Inventoteca/DisplayErgonomia/Diagramas/DiagramaDisplayErgonomia.png

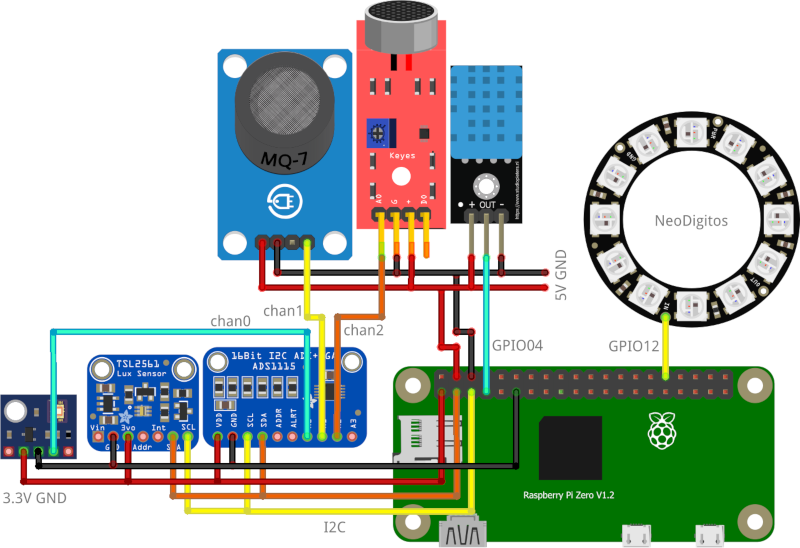
Diagramas/DiagramaDisplayErgonomia.png
