Inventoteca/DisplayErgonomia/Fotos/34:94:54:C7:D3:98.png

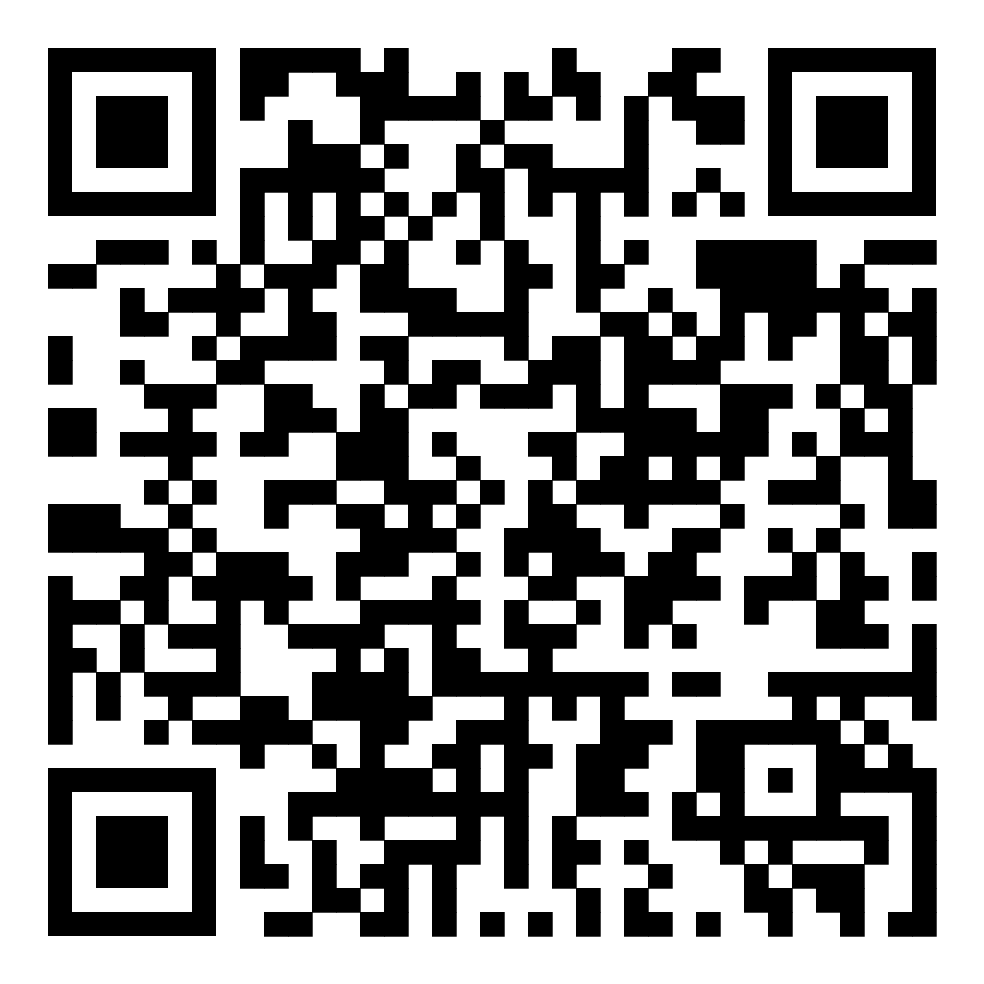
Fotos/34:94:54:C7:D3:98.png
