Inventoteca/DisplayErgonomia/Fotos/Dibujo ventanas en la parte superior.jpg

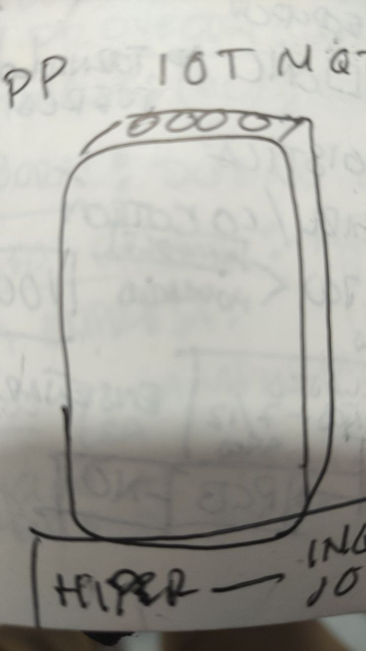
Fotos/Dibujo ventanas en la parte superior.jpg
