Inventoteca/DisplayErgonomia/Fotos/Doble capa MDF.jpg

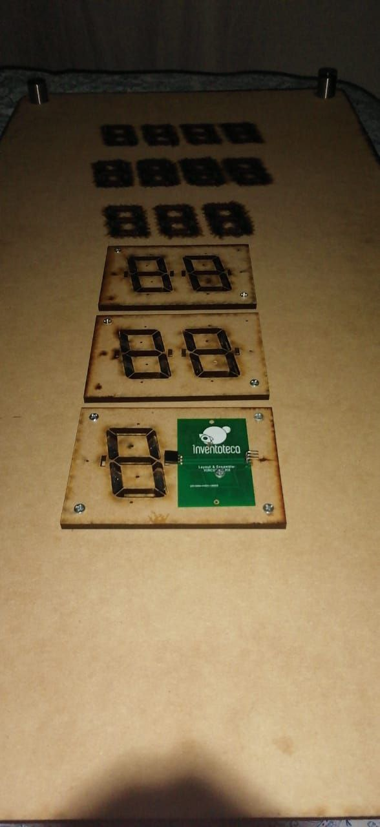
Fotos/Doble capa MDF.jpg
