Inventoteca/DisplayErgonomia/Fotos/E05A1B560F74.png

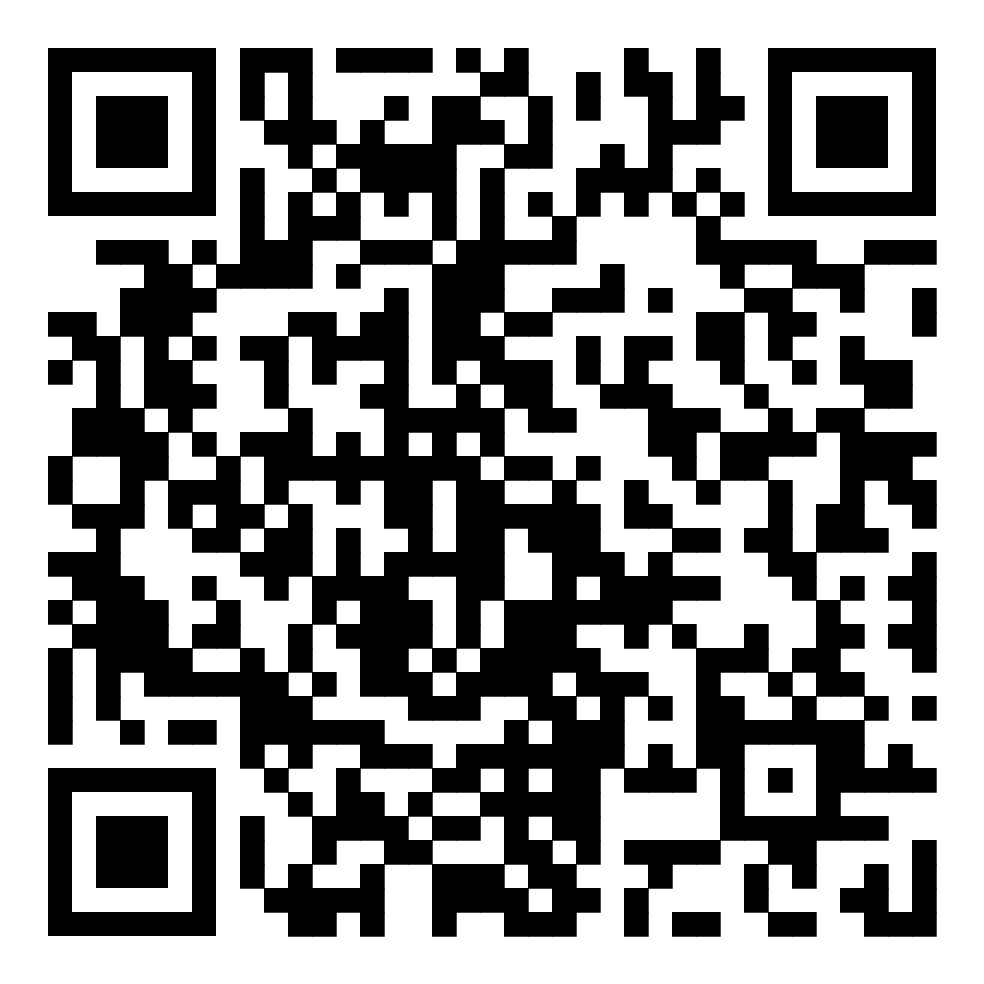
Fotos/E05A1B560F74.png
