Inventoteca/DisplayErgonomia/Fotos/E05A1B561050.png

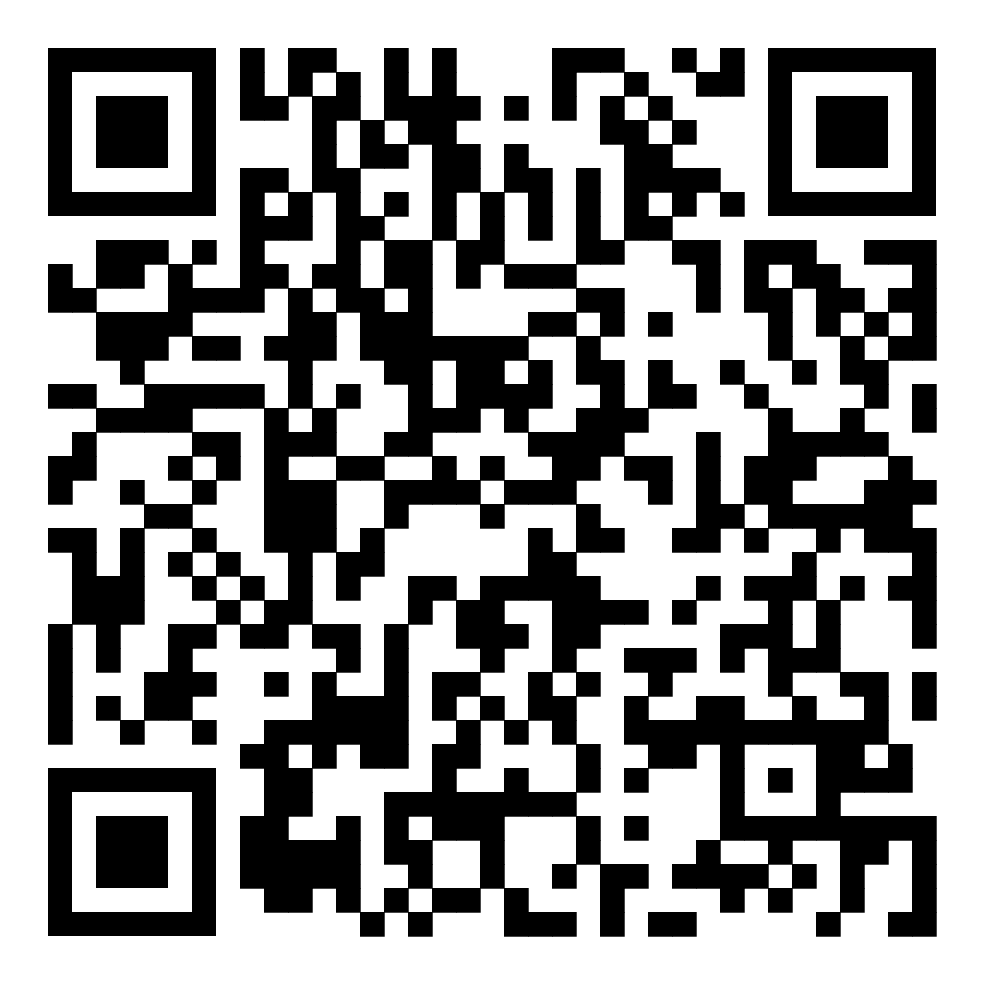
Fotos/E05A1B561050.png
