Inventoteca/DisplayErgonomia/Fotos/photo_5015306214770322337_y.jpg

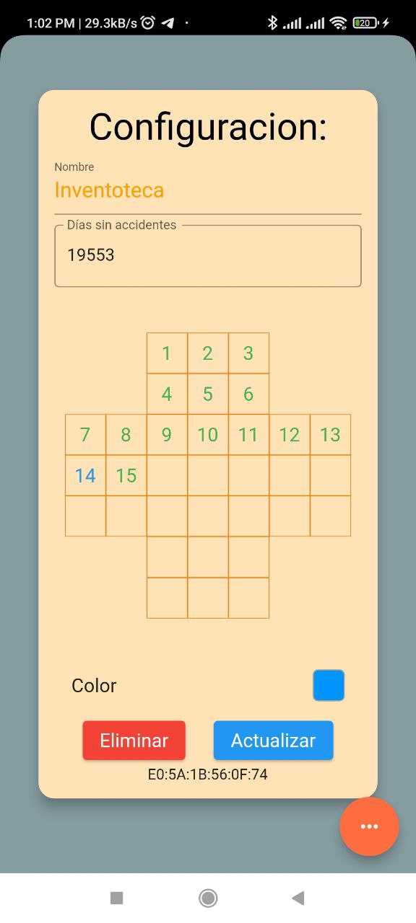
Fotos/photo_5015306214770322337_y.jpg
