Inventoteca/DisplayErgonomia/Fotos/photo_5015306214770322338_y.jpg

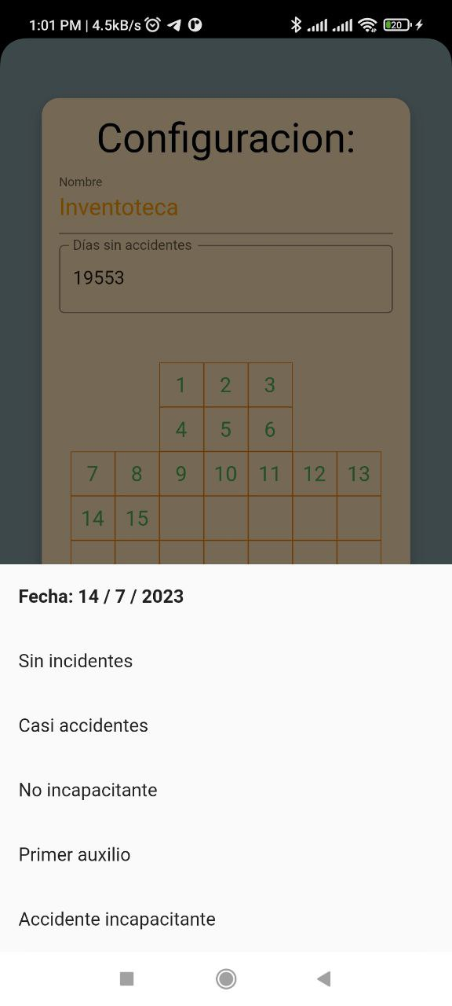
Fotos/photo_5015306214770322338_y.jpg
