Inventoteca/DisplayErgonomia/Fotos/photo_5015306214770322340_y.jpg

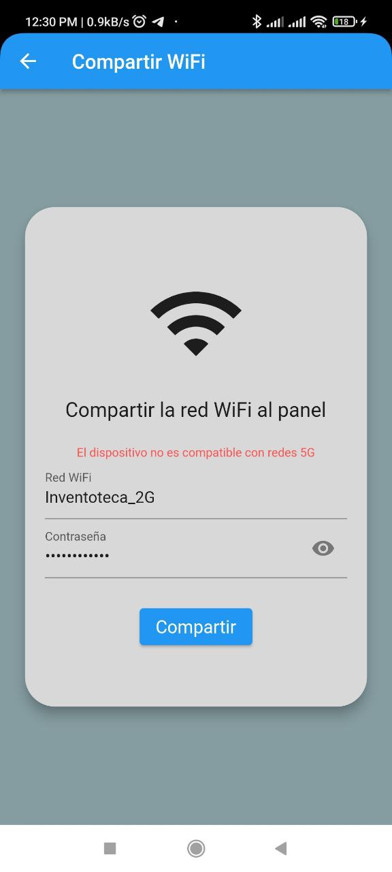
Fotos/photo_5015306214770322340_y.jpg
