Inventoteca/DisplayErgonomia/Fotos/photo_5015306214770322341_y.jpg

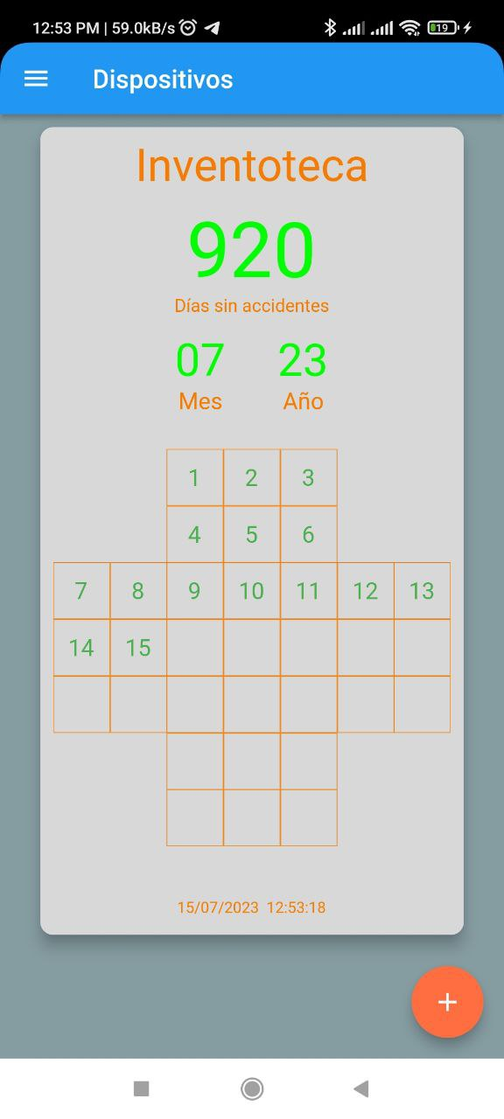
Fotos/photo_5015306214770322341_y.jpg
