Inventoteca/DisplayErgonomia/Fotos/photo_5015306214770322343_y.jpg

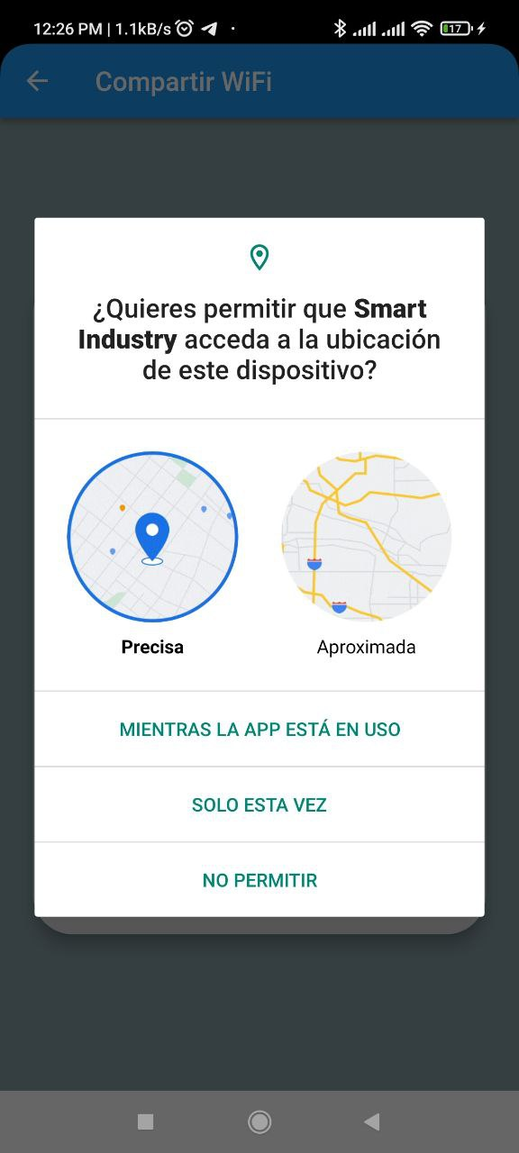
Fotos/photo_5015306214770322343_y.jpg
