Inventoteca/DisplayErgonomia/Fotos/photo_5015306214770322344_y.jpg

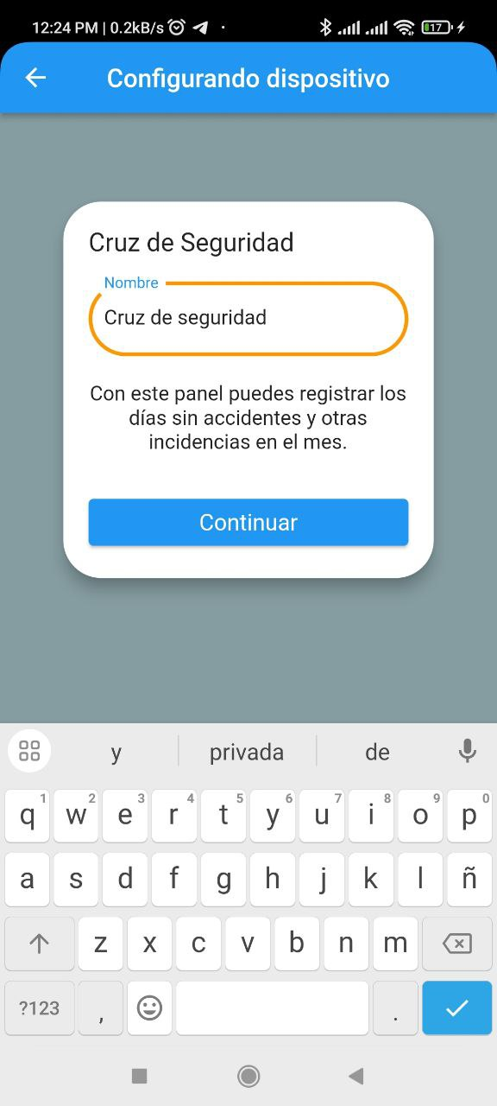
Fotos/photo_5015306214770322344_y.jpg
