Inventoteca/DisplayErgonomia/Fotos/photo_5015306214770322345_y.jpg

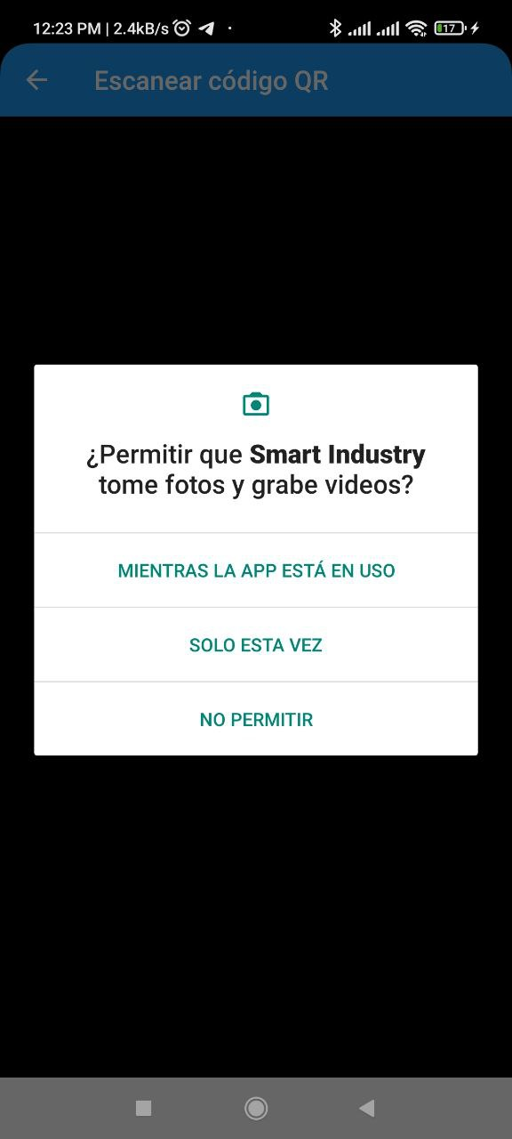
Fotos/photo_5015306214770322345_y.jpg
