Inventoteca/DisplayErgonomia/Fotos/photo_5015306214770322346_y.jpg

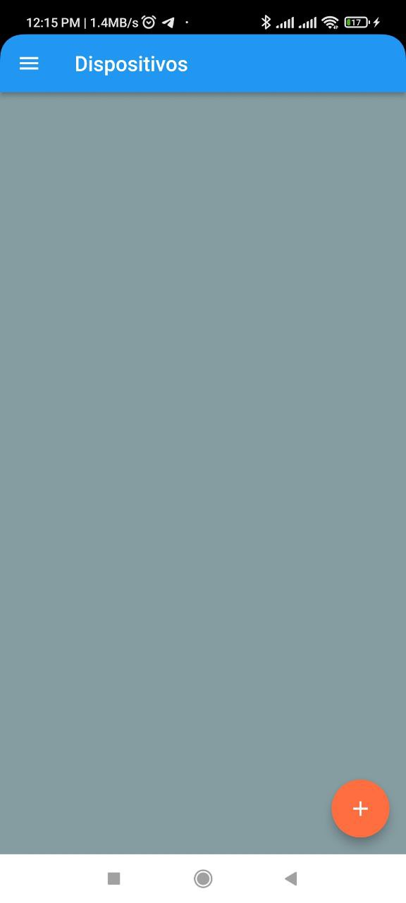
Fotos/photo_5015306214770322346_y.jpg
