Inventoteca/DisplayErgonomia/Fotos/photo_5015306214770322347_y.jpg

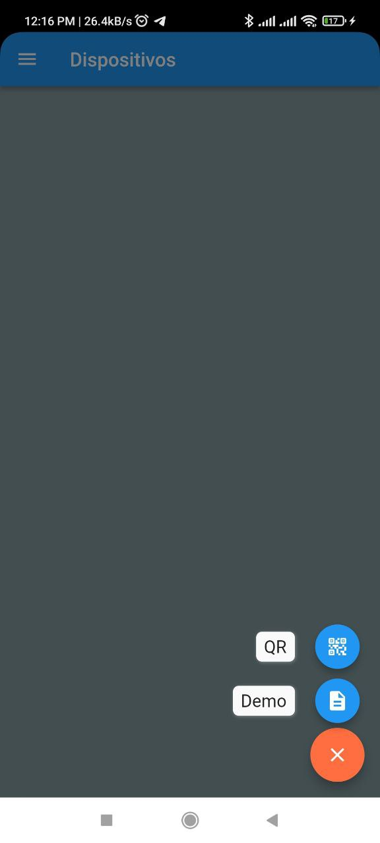
Fotos/photo_5015306214770322347_y.jpg
