Inventoteca/DisplayErgonomia/Fotos/photo_5015306214770322348_y.jpg

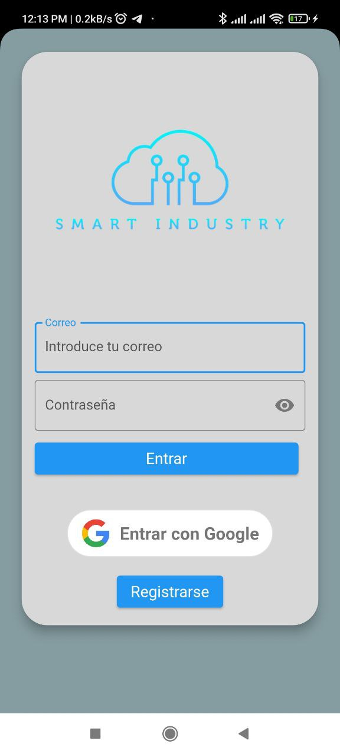
Fotos/photo_5015306214770322348_y.jpg
