Inventoteca/DisplayErgonomia/Fotos/Probando_sensores_con_Arduino/20210329_135027.jpg

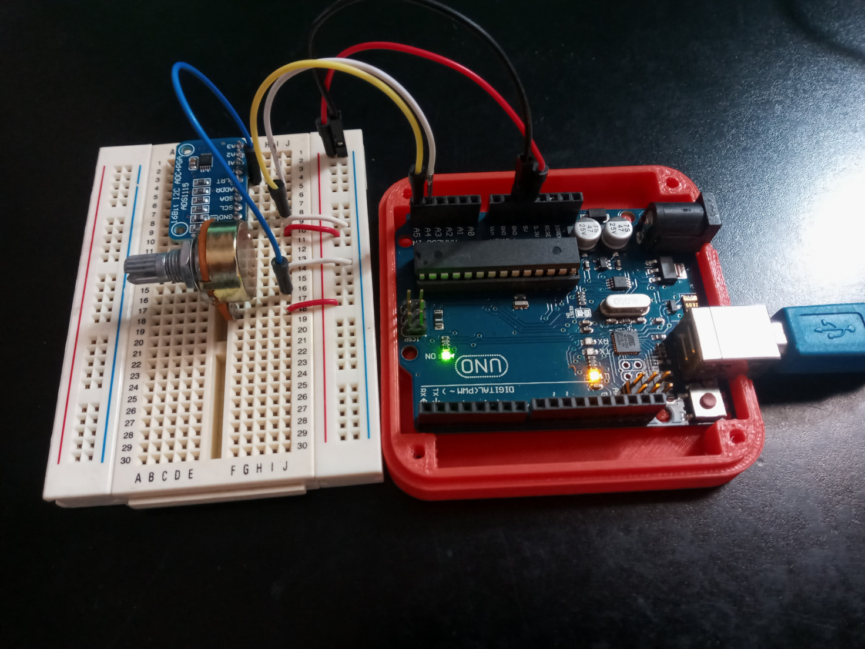
Fotos/Probando_sensores_con_Arduino/20210329_135027.jpg
