Inventoteca/DisplayErgonomia/Fotos/Probando_sensores_con_Arduino/20210329_150442.jpg

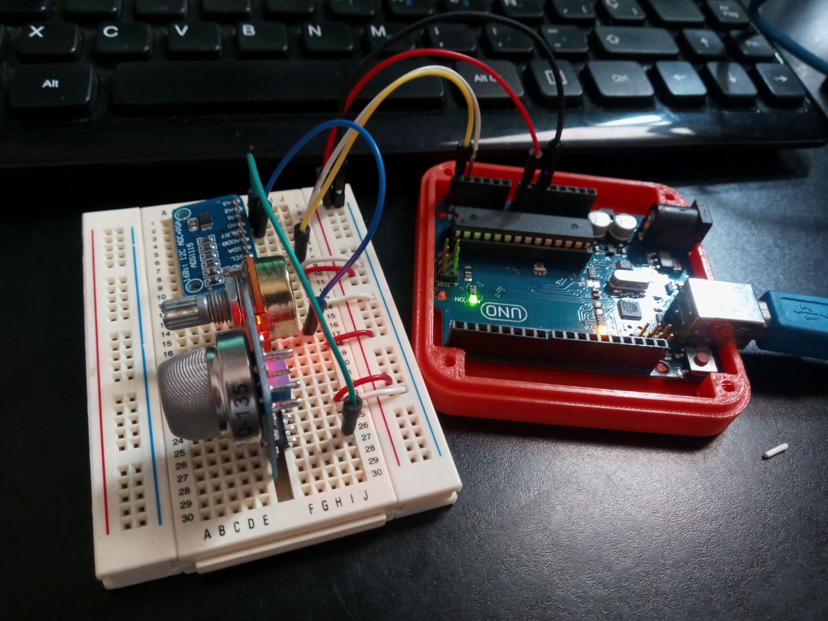
Fotos/Probando_sensores_con_Arduino/20210329_150442.jpg
