Inventoteca/DisplayErgonomia/Fotos/Probando_sensores_con_Arduino/20210329_164652.jpg

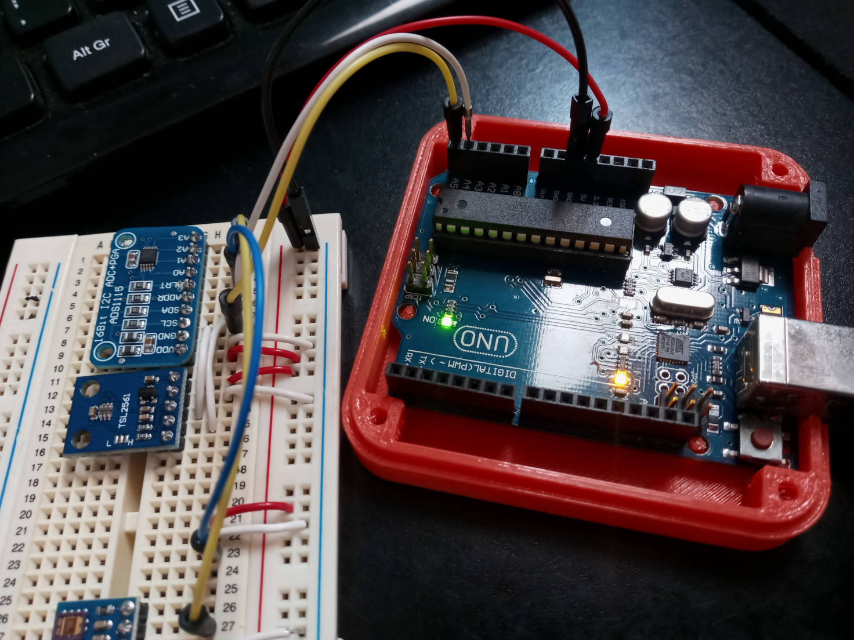
Fotos/Probando_sensores_con_Arduino/20210329_164652.jpg
