Inventoteca/DisplayErgonomia/Fotos/qr.png

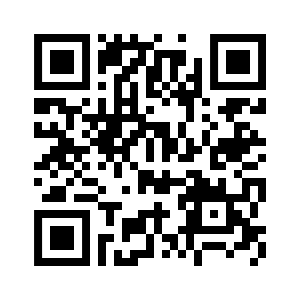
Fotos/qr.png
