Inventoteca/DisplayErgonomia/Fotos/rangos_y_colores.jpg

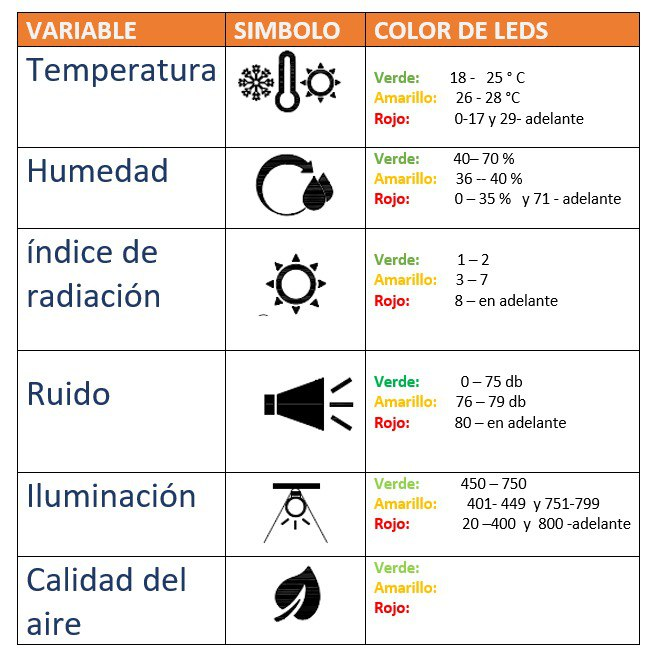
Fotos/rangos_y_colores.jpg
