Inventoteca/DisplayErgonomia/Fotos/Smart (1).png

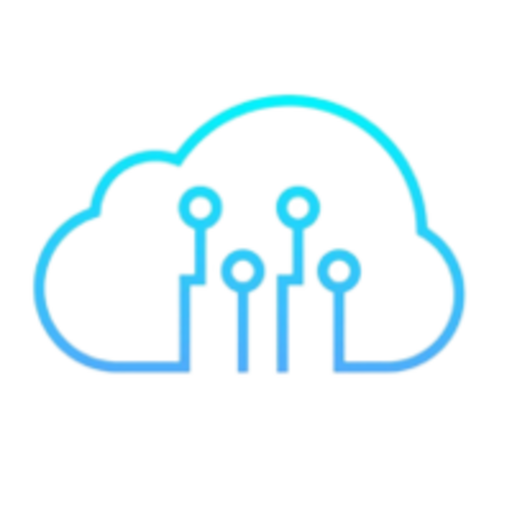
Fotos/Smart (1).png
