Inventoteca/DisplayErgonomia/Fotos/SmartIndustry.png

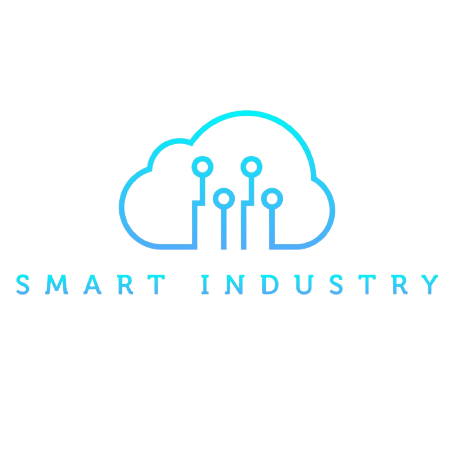
Fotos/SmartIndustry.png
