Inventoteca/DisplayErgonomia/Fotos/Vista frontal.jpg

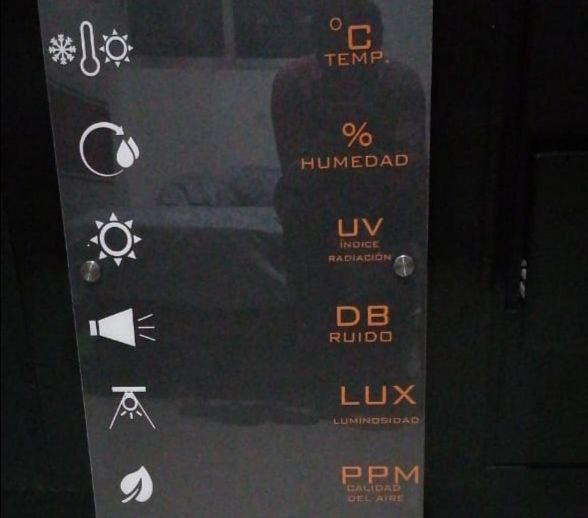
Fotos/Vista frontal.jpg
