Inventoteca/DisplayErgonomia/Programa/Capturas/ADS1115 con Arduino.png

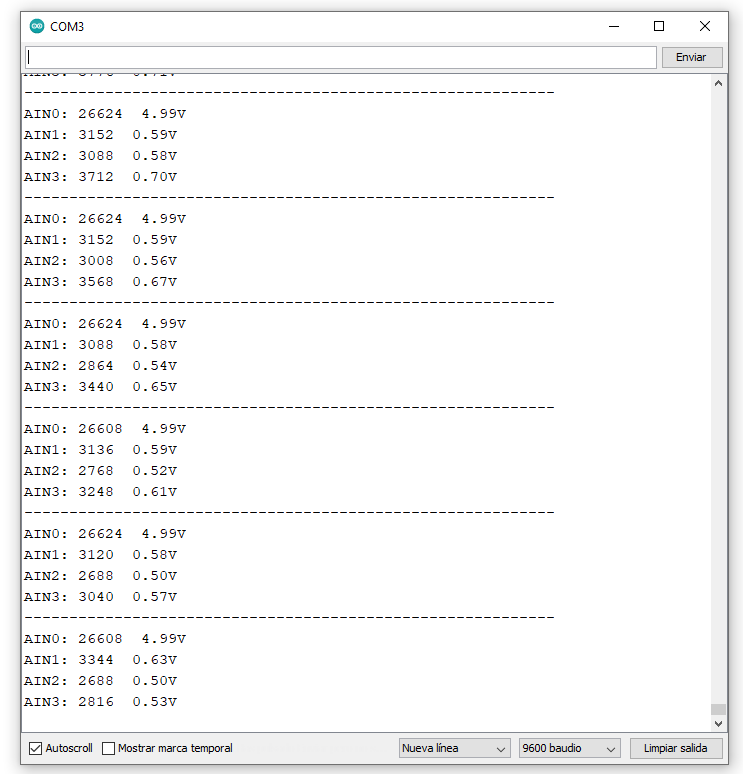
Programa/Capturas/ADS1115 con Arduino.png
