Inventoteca/DisplayErgonomia/Programa/Capturas/Captura de pantalla 2021-03-29 205107.png

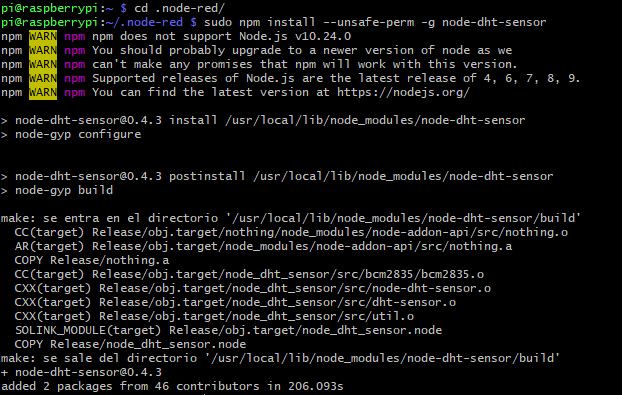
Programa/Capturas/Captura de pantalla 2021-03-29 205107.png
