Inventoteca/DisplayErgonomia/Programa/Capturas/flujo funcionando.png

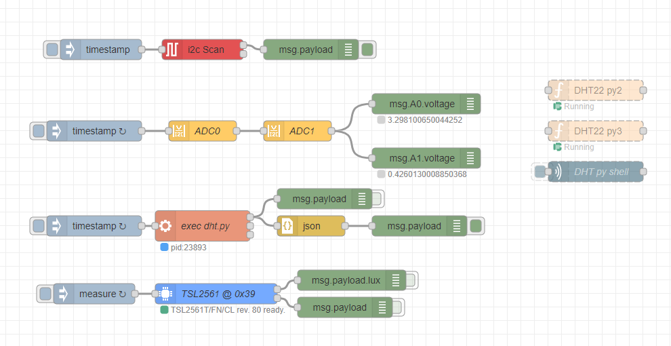
Programa/Capturas/flujo funcionando.png
