Inventoteca/DisplayErgonomia/Programa/Capturas/flujo, no ha funcionado dht, empezar a probar tsl2561.png

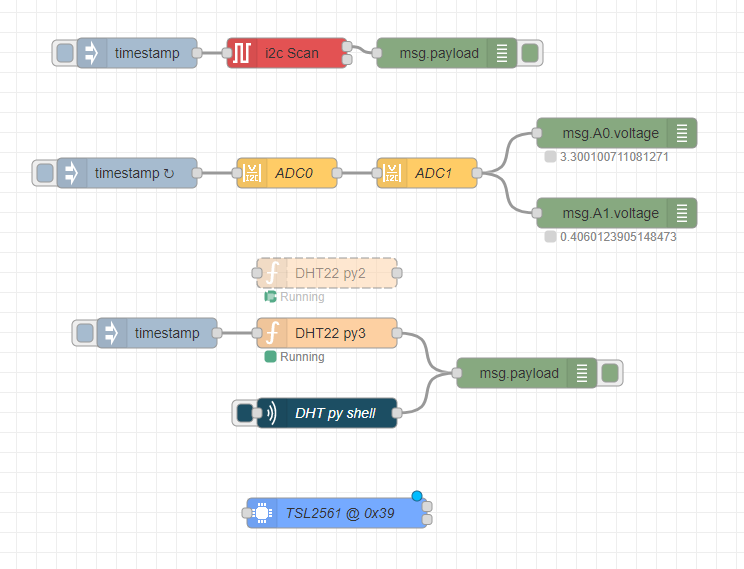
Programa/Capturas/flujo, no ha funcionado dht, empezar a probar tsl2561.png
