Inventoteca/DisplayErgonomia/Programa/Capturas/Librerías para ADS1115.png

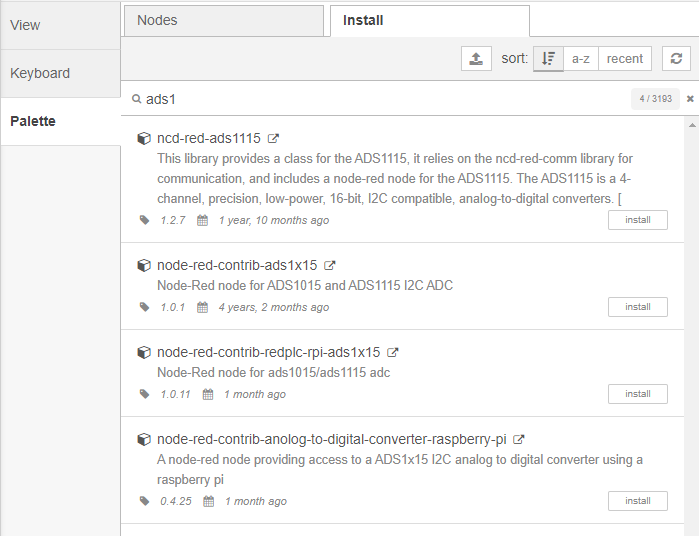
Programa/Capturas/Librerías para ADS1115.png
