Inventoteca/DisplayErgonomia/Programa/Capturas/Librerías para DHT22.png

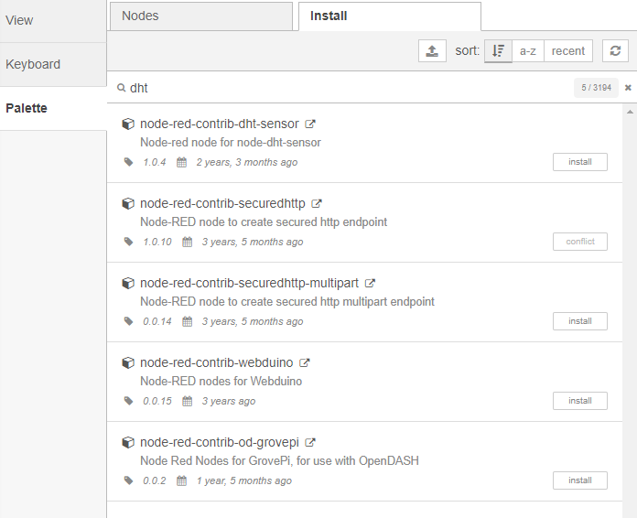
Programa/Capturas/Librerías para DHT22.png
