Inventoteca/DisplayErgonomia/Programa/Capturas/Librerías para TSL2561.png

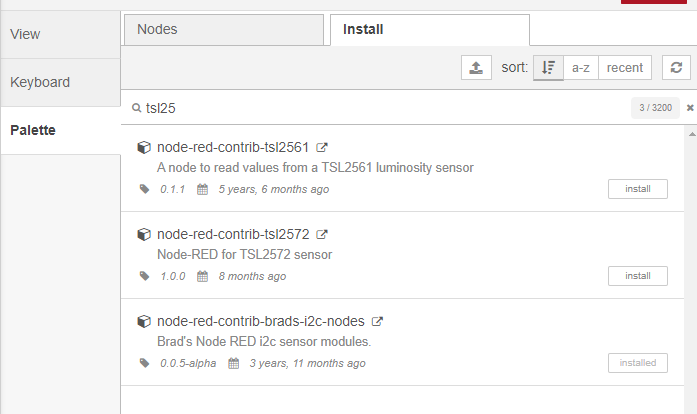
Programa/Capturas/Librerías para TSL2561.png
