Inventoteca/DisplayErgonomia/Programa/Capturas/nodos python instalados.png

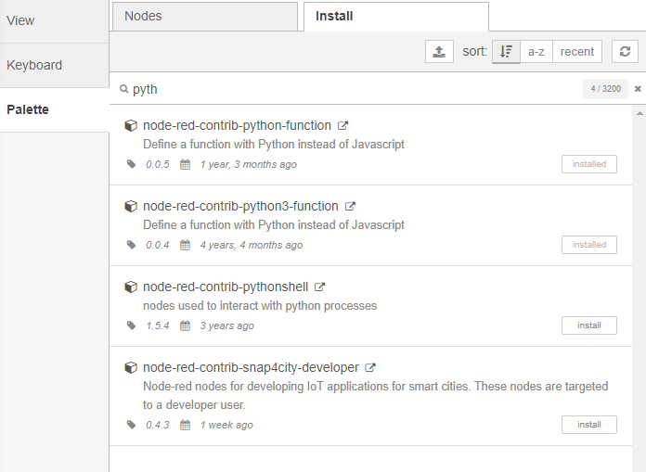
Programa/Capturas/nodos python instalados.png
