Inventoteca/DisplayErgonomia/Programa/Capturas/nr flujos y cred.png

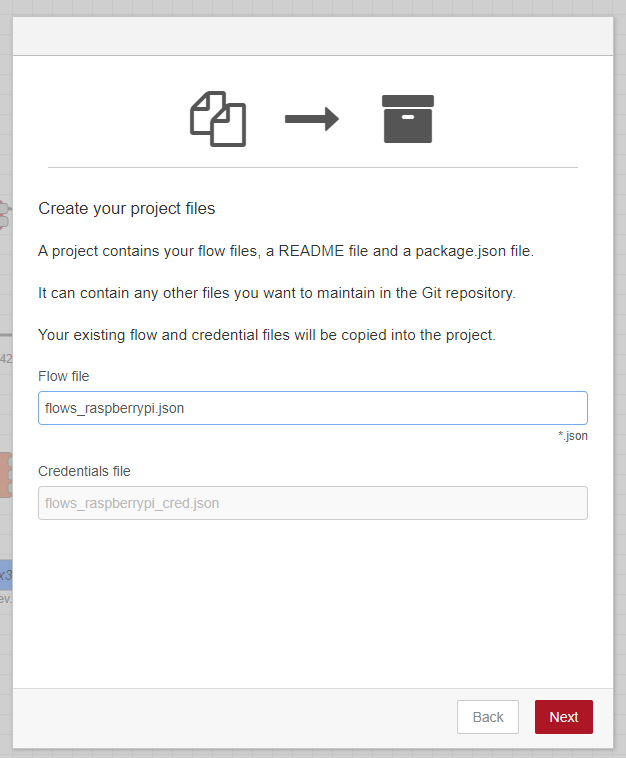
Programa/Capturas/nr flujos y cred.png
