Inventoteca/DisplayErgonomia/Programa/Capturas/nr proy.png

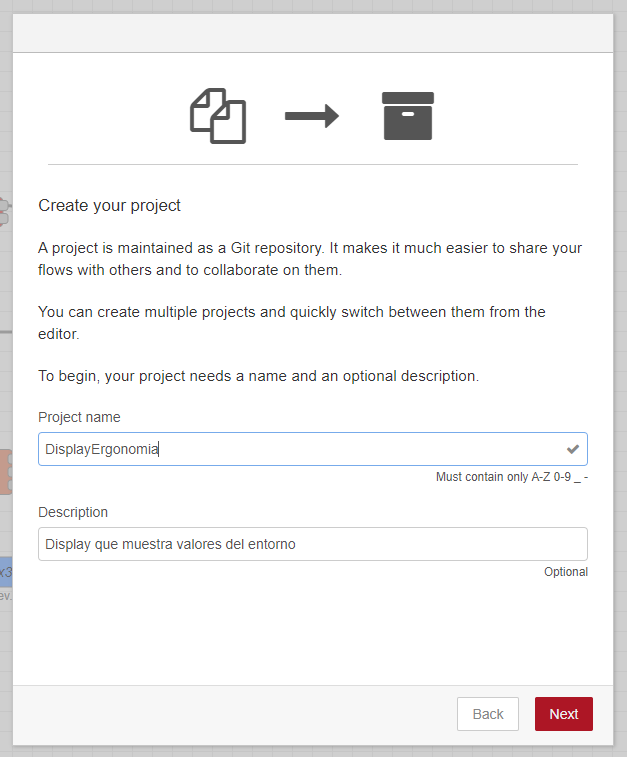
Programa/Capturas/nr proy.png
