Inventoteca/DisplayErgonomia/Programa/Capturas/nr proyecto creado.png

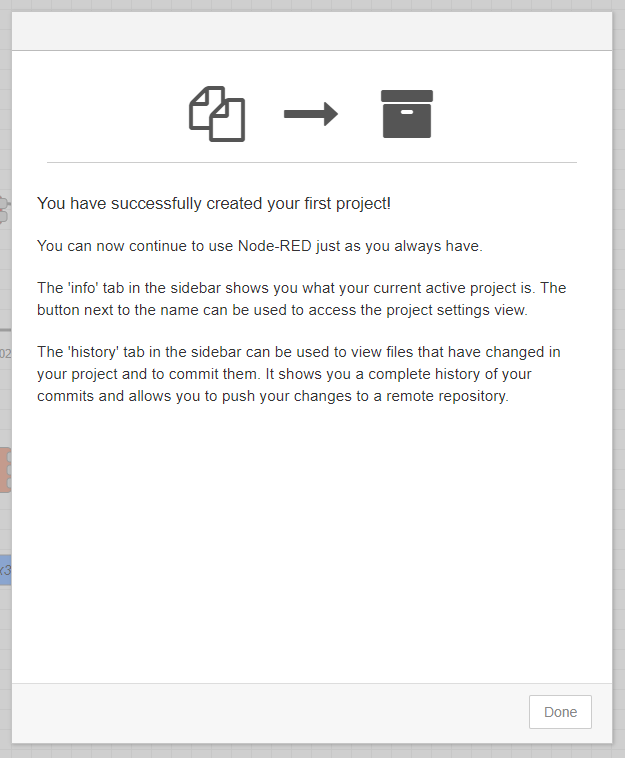
Programa/Capturas/nr proyecto creado.png
