Inventoteca/DisplayErgonomia/Programa/Capturas/nr sin ecrip.png

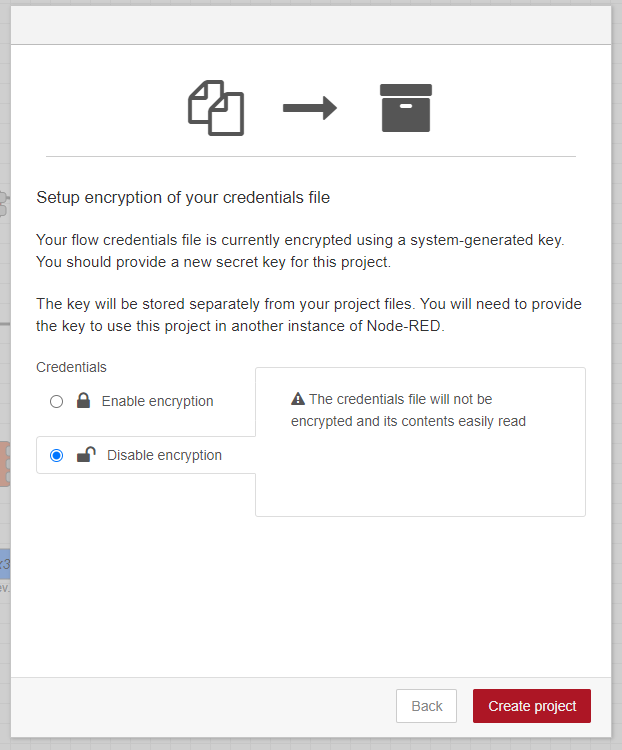
Programa/Capturas/nr sin ecrip.png
