Inventoteca/DisplayErgonomia/Programa/Capturas/nr usuario.png

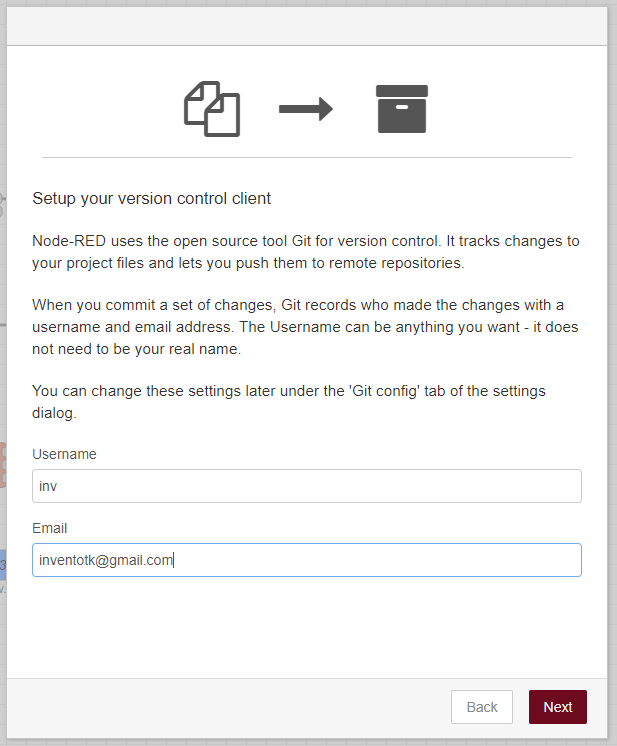
Programa/Capturas/nr usuario.png
