Inventoteca/DisplayErgonomia/Programa/Capturas/push to main.png

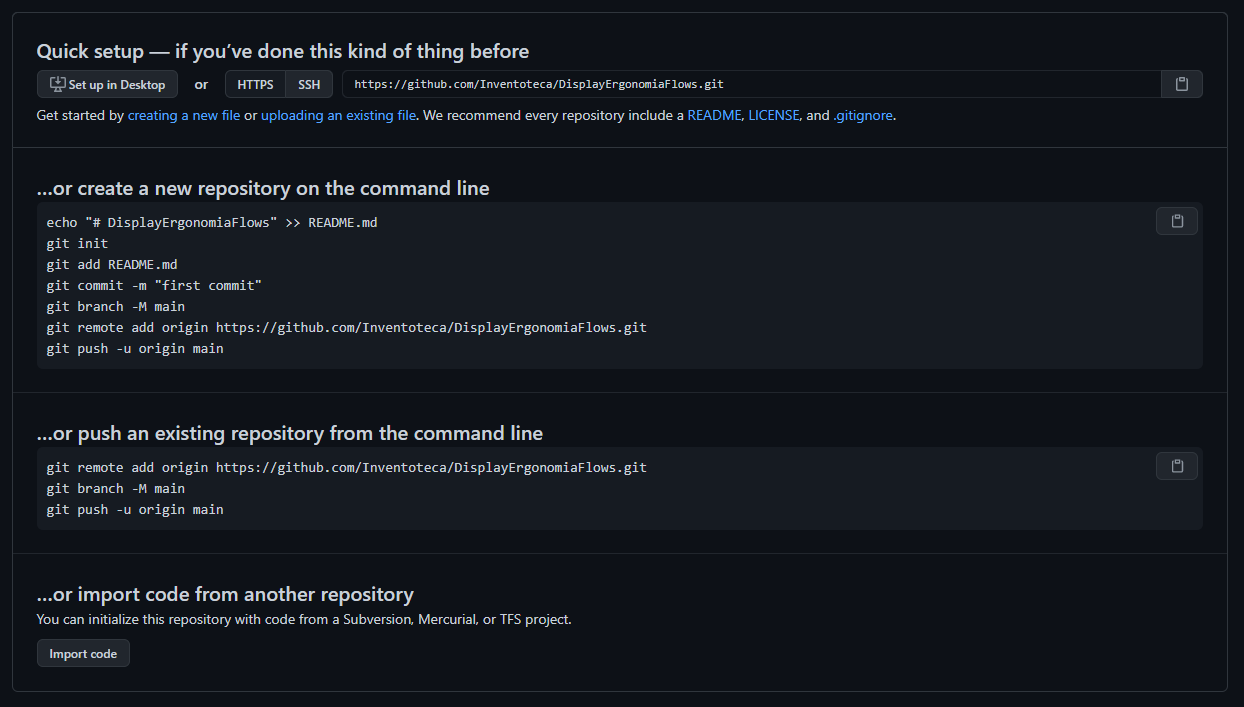
Programa/Capturas/push to main.png
