Inventoteca/DisplayErgonomia/Programa/Capturas/tsl2561 si jala.png

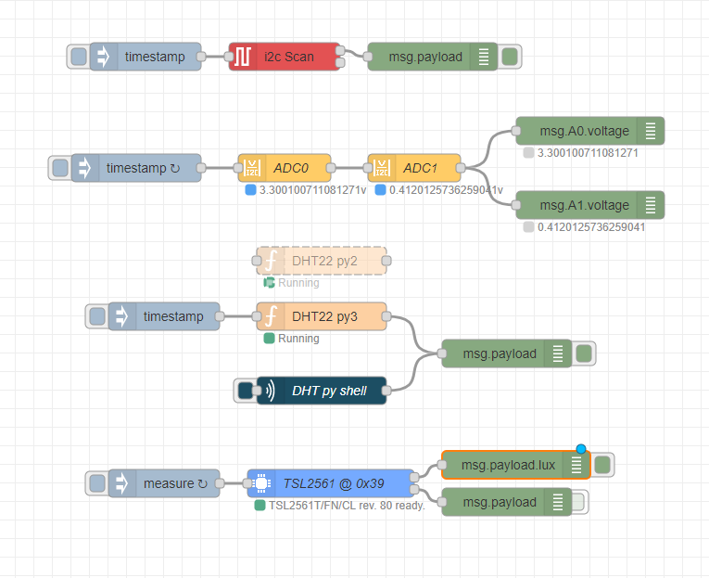
Programa/Capturas/tsl2561 si jala.png
