Inventoteca/DisplayErgonomia/Diseños/corte_laser/pasado/2digitos/2digitos_mdf3mm_126x202.dxf

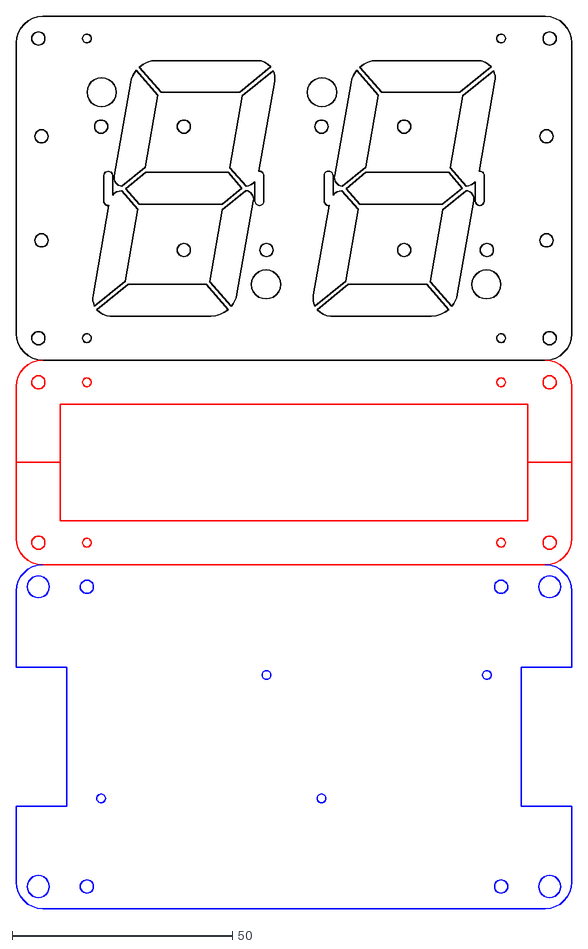
[picture p60: CAD file, 2021-03-31]
Diseños/corte_laser/pasado/2digitos/2digitos_mdf3mm_126x202.dxf
126.0 x 202.4
