Inventoteca/DisplayErgonomia/Diseños/corte_laser/pasado/3digitos/3digitos_mdf3mm_176x202.dxf

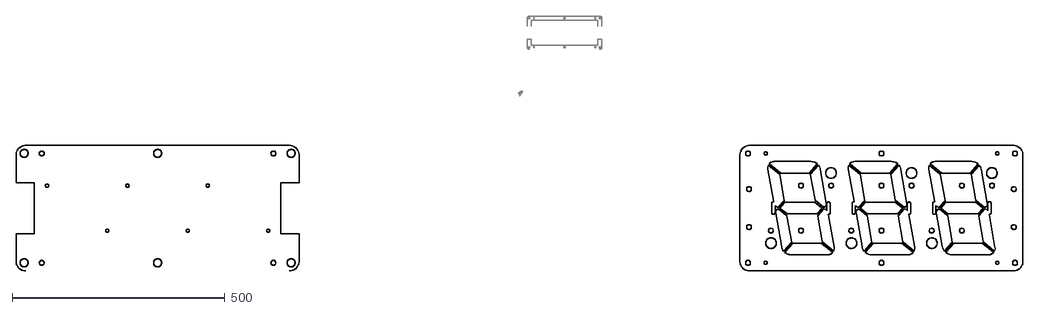
[picture p61: CAD file, 2021-03-31]
Diseños/corte_laser/pasado/3digitos/3digitos_mdf3mm_176x202.dxf
2366.0 x 598.5
