Inventoteca/DisplayErgonomia/Diseños/corte_laser/pasado/4digitos/4digitos_mdf3mm_226x202.dxf

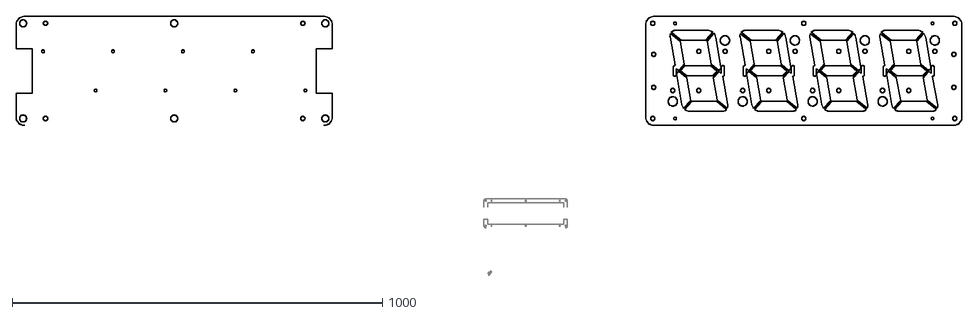
[picture p62: CAD file, 2021-03-31]
Diseños/corte_laser/pasado/4digitos/4digitos_mdf3mm_226x202.dxf
2555.0 x 700.4
