Inventoteca/DisplayErgonomia/Diseños/STL/clip.stl

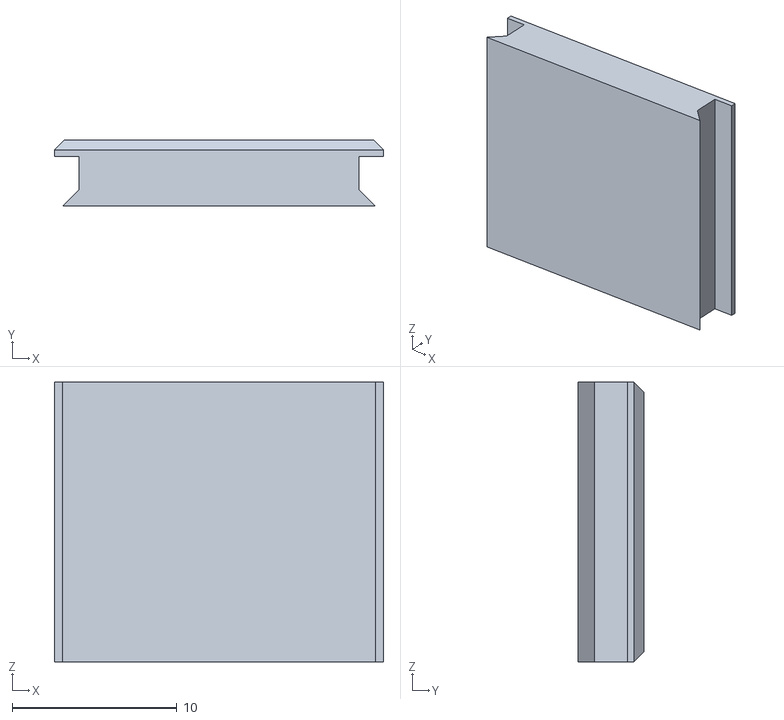
[picture p63: CAD file, 2021-07-01]
Diseños/STL/clip.stl
20.0 x 4.00 x 17.0
