Inventoteca/DisplayErgonomia/Diseños/STL/tapasen.stl

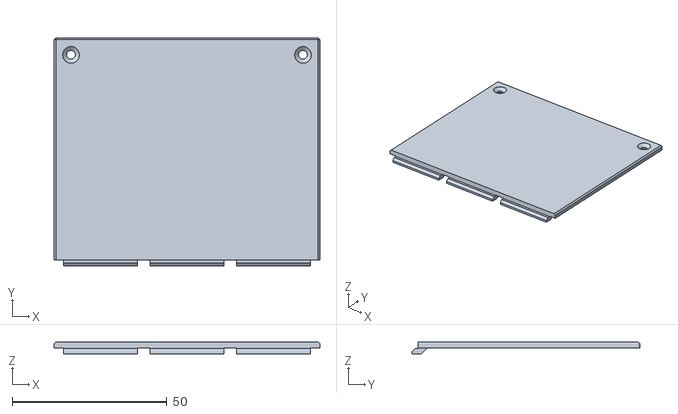
[picture p64: CAD file, 2021-07-01]
Diseños/STL/tapasen.stl
86.0 x 73.8 x 4.00
