Inventoteca/DisplayErgonomia/Diseños/STL/sopext2.stl

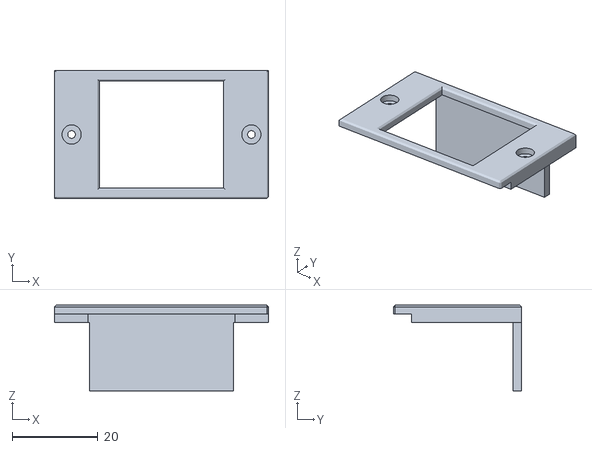
[picture p65: CAD file, 2021-07-01]
Diseños/STL/sopext2.stl
50.0 x 30.0 x 20.0
