Inventoteca/DisplayErgonomia/Fotos/Ensamblando_display/20210401_191805.jpg

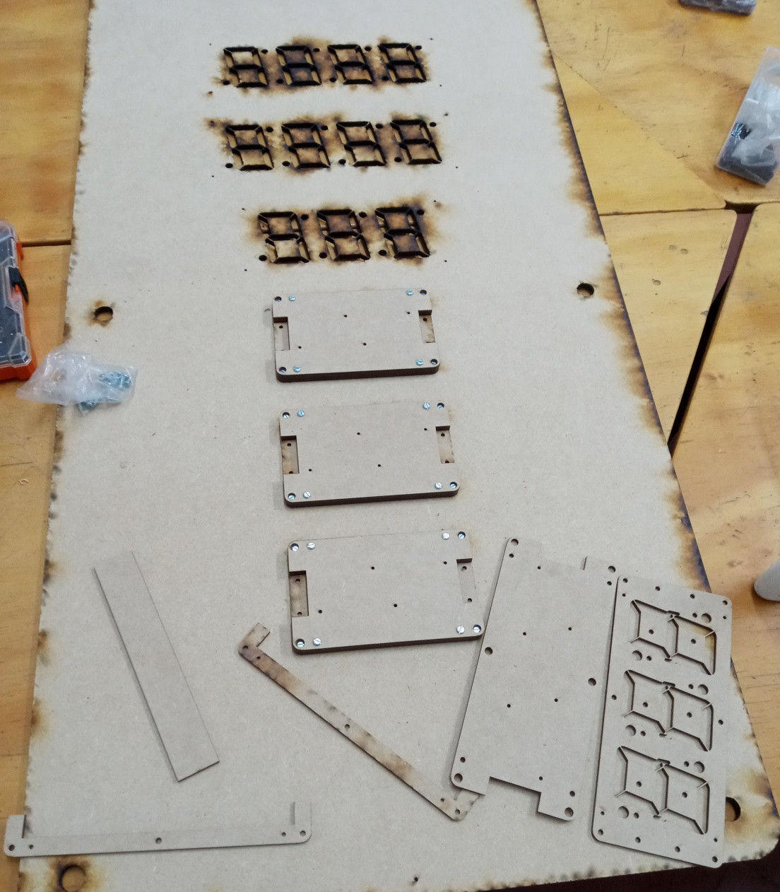
Fotos/Ensamblando_display/20210401_191805.jpg
