Inventoteca/DisplayErgonomia/Fotos/Ensamblando_display/20210401_191921.jpg

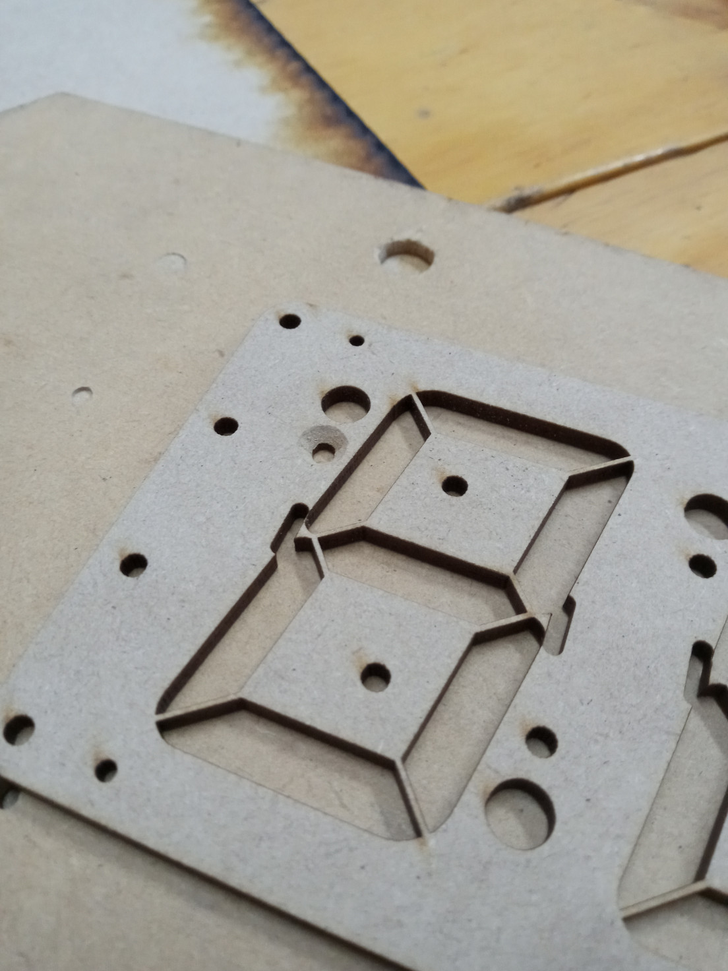
Fotos/Ensamblando_display/20210401_191921.jpg
