Inventoteca/DisplayErgonomia/Fotos/Ensamblando_display/20210401_191934.jpg

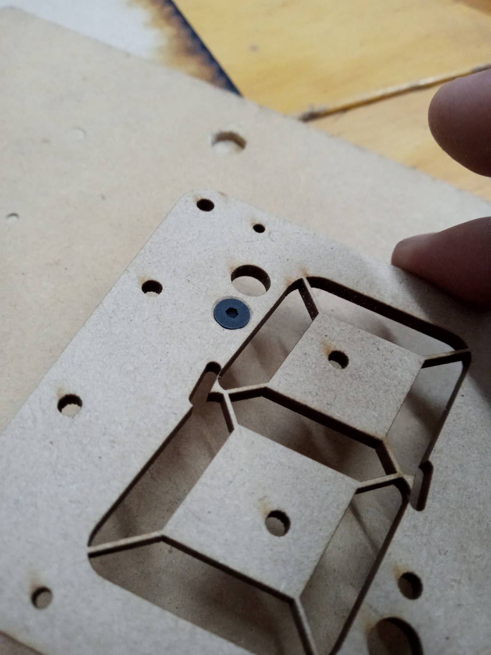
Fotos/Ensamblando_display/20210401_191934.jpg
