Inventoteca/DisplayErgonomia/Fotos/Ensamblando_display/20210401_192517.jpg

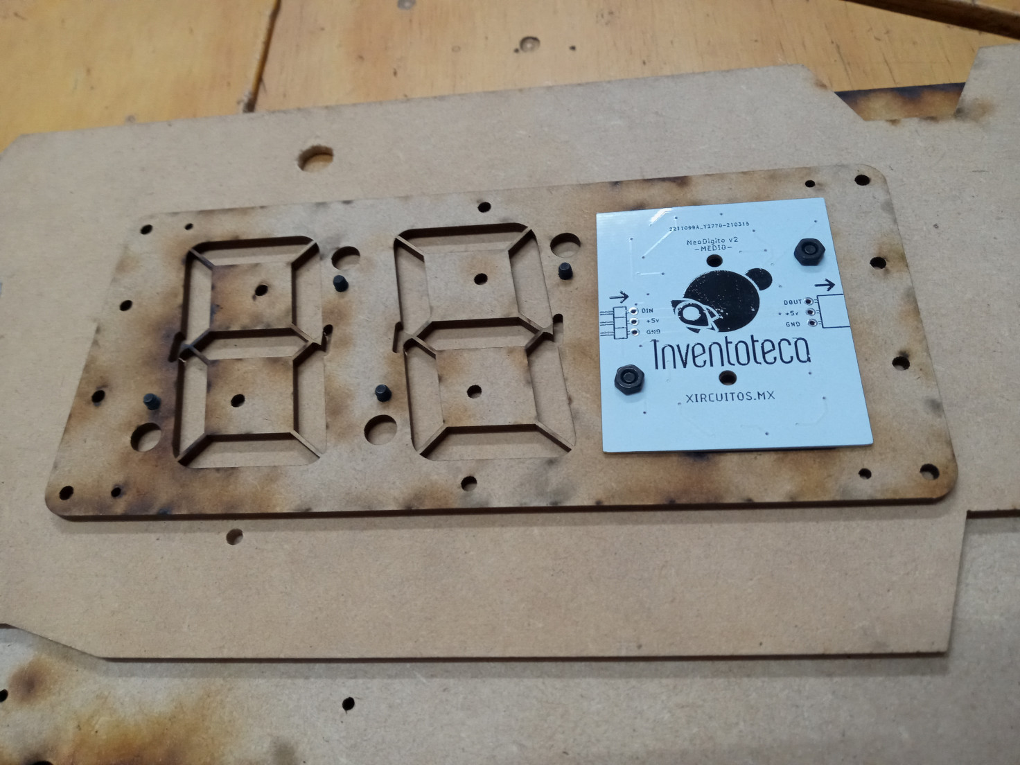
Fotos/Ensamblando_display/20210401_192517.jpg
