Inventoteca/DisplayErgonomia/Fotos/Ensamblando_display/20210401_193449.jpg

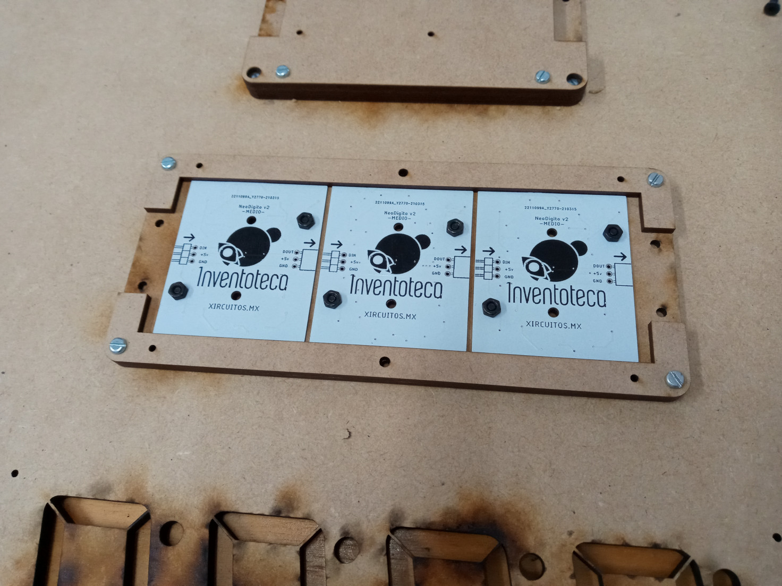
Fotos/Ensamblando_display/20210401_193449.jpg
