Inventoteca/DisplayErgonomia/Fotos/Ensamblando_display/20210401_193509.jpg

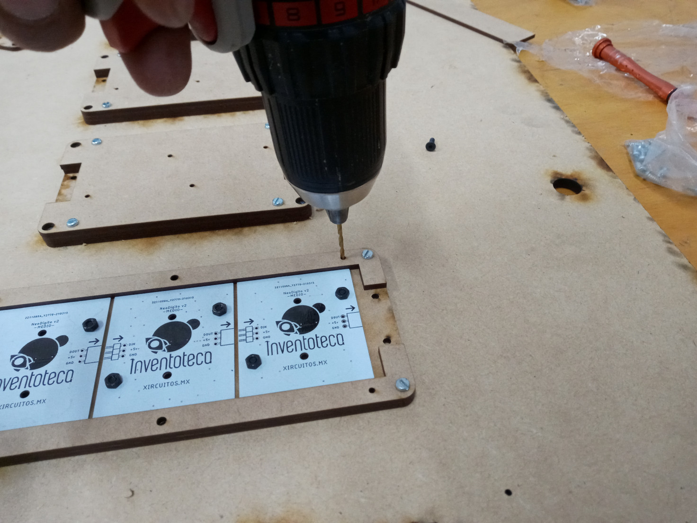
Fotos/Ensamblando_display/20210401_193509.jpg
