Inventoteca/DisplayErgonomia/Fotos/Ensamblando_display/20210401_194448.jpg

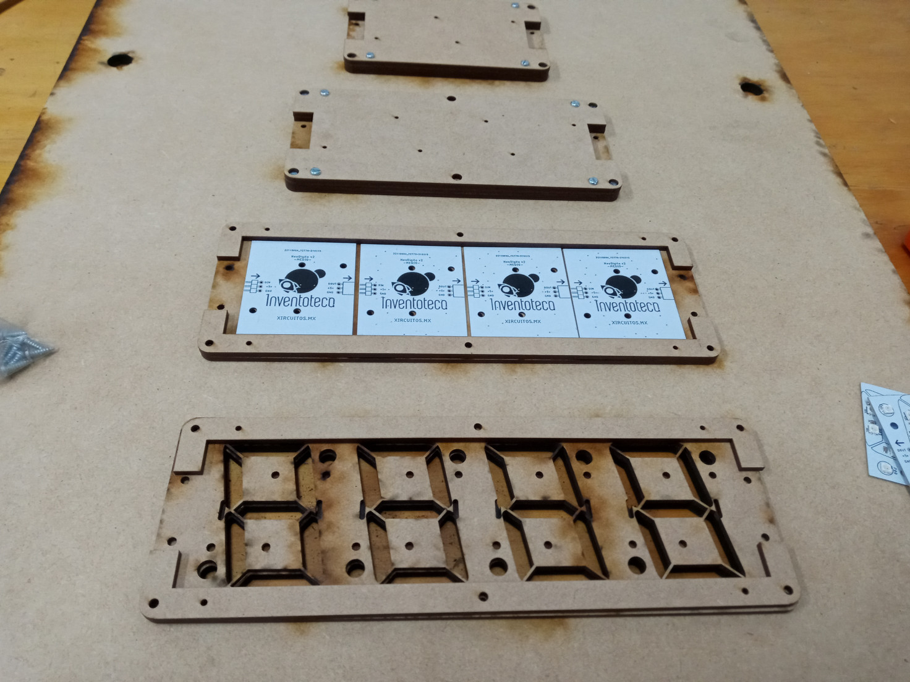
Fotos/Ensamblando_display/20210401_194448.jpg
