Inventoteca/DisplayErgonomia/Fotos/Ensamblando_display/20210401_200822.jpg

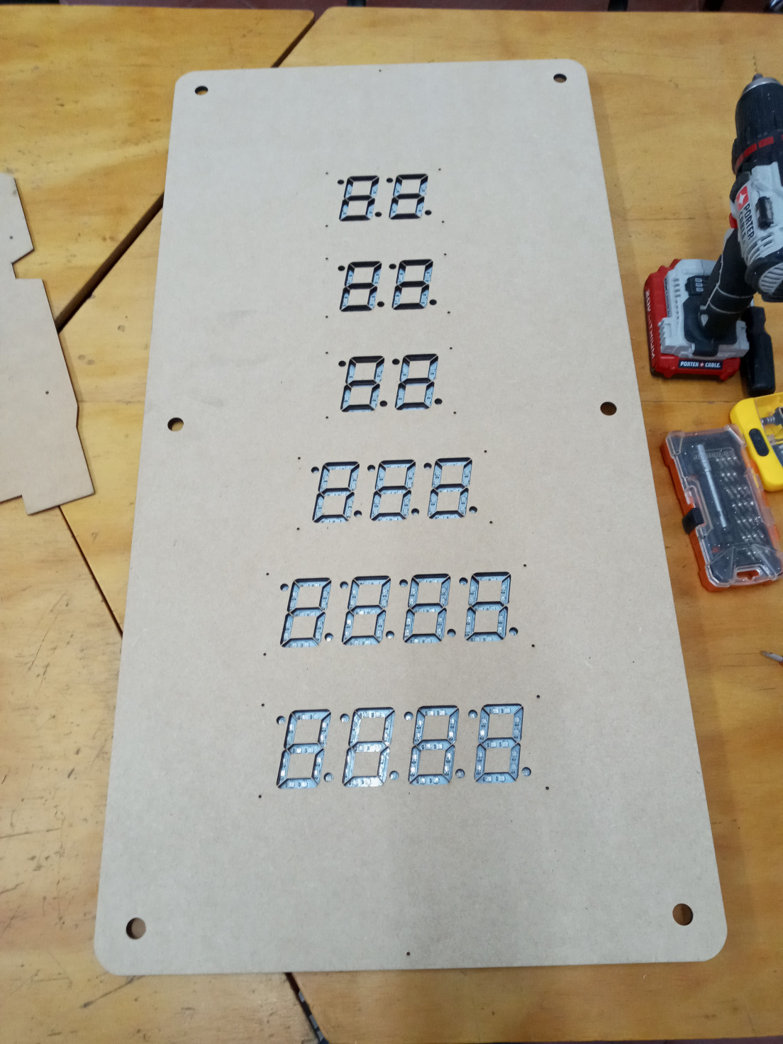
Fotos/Ensamblando_display/20210401_200822.jpg
