Inventoteca/DisplayErgonomia/Fotos/Ensamblando_display/20210405_124439.jpg

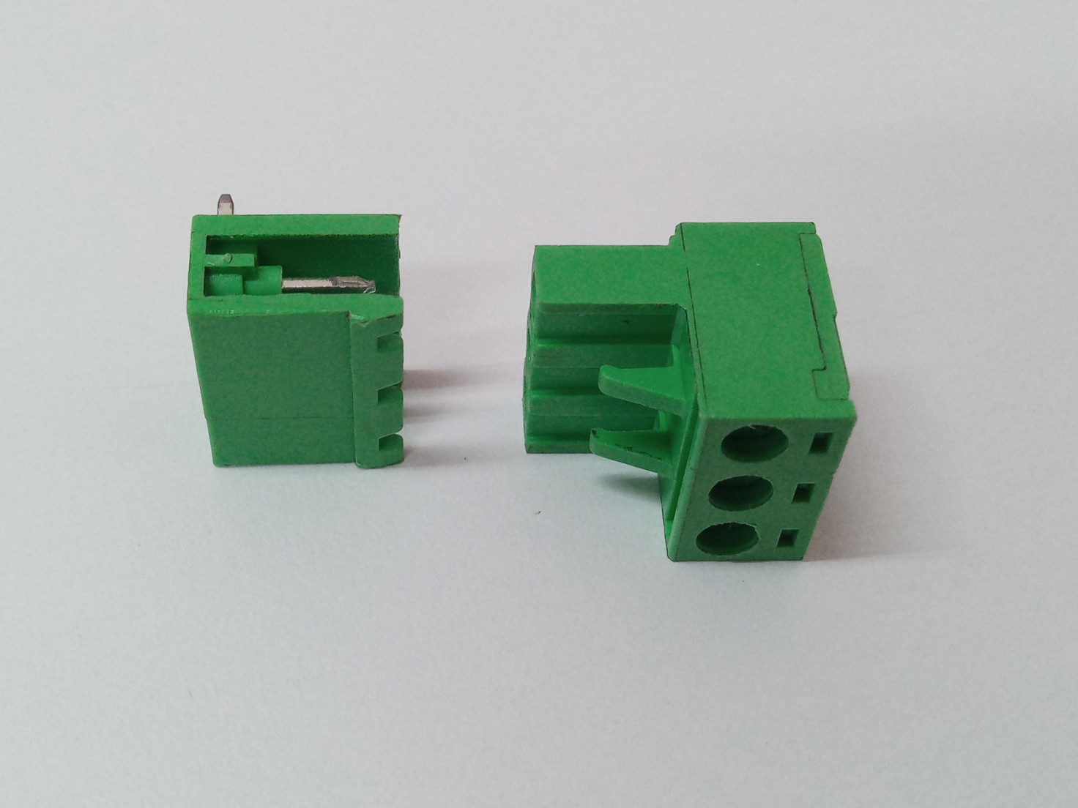
Fotos/Ensamblando_display/20210405_124439.jpg
