Inventoteca/DisplayErgonomia/Fotos/Ensamblando_display/20210406_154444.jpg

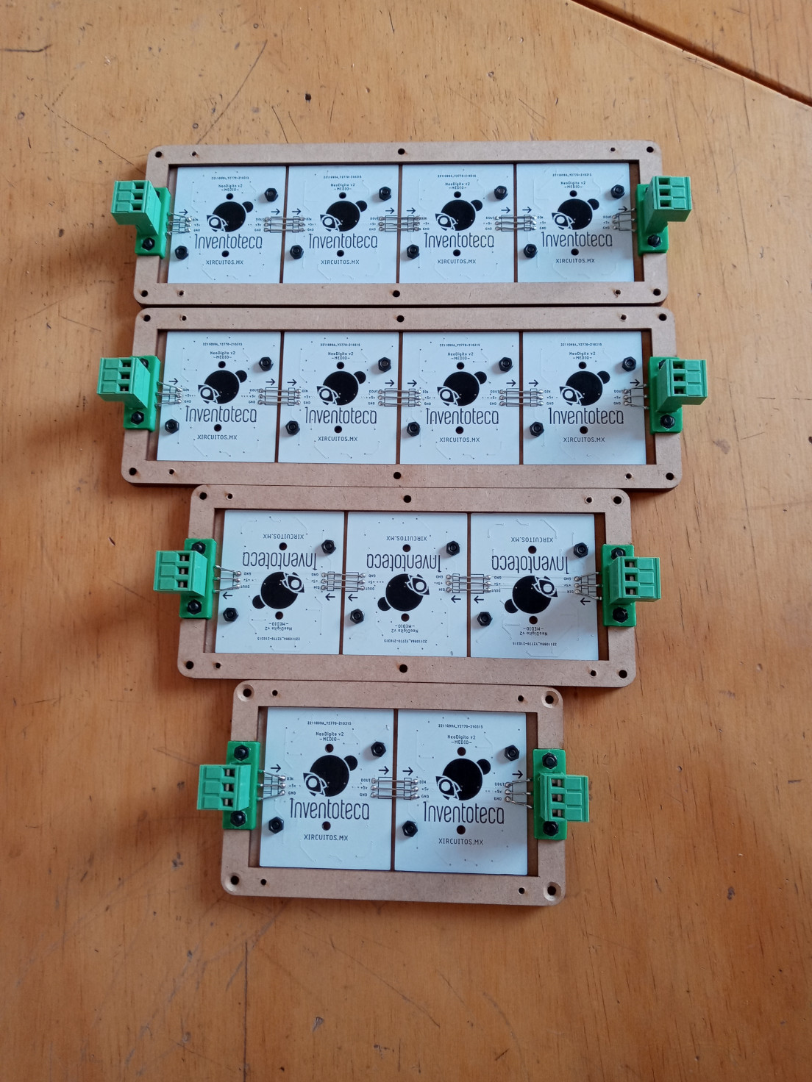
Fotos/Ensamblando_display/20210406_154444.jpg
