Inventoteca/DisplayErgonomia/Fotos/Ensamblando_display/20210406_171642.jpg

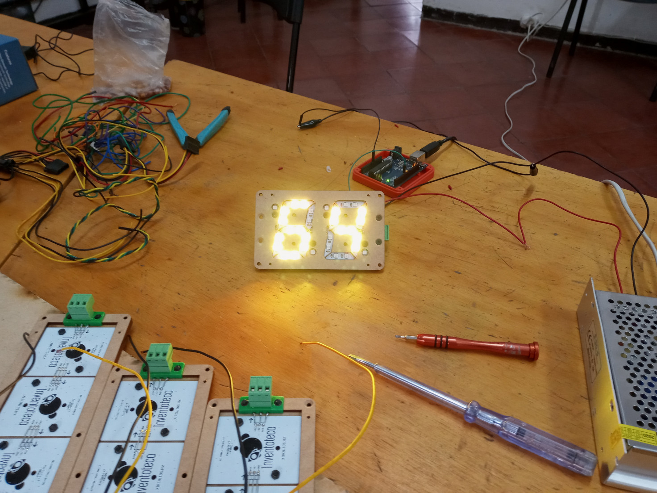
Fotos/Ensamblando_display/20210406_171642.jpg
