Inventoteca/DisplayErgonomia/Fotos/Ensamblando_display/20210406_193103.jpg

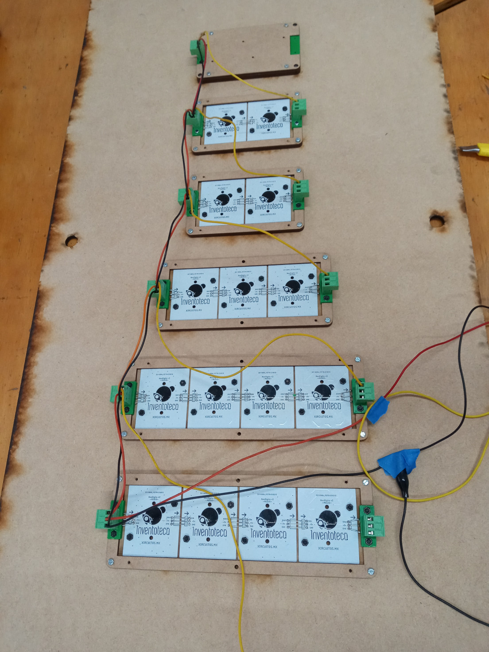
Fotos/Ensamblando_display/20210406_193103.jpg
