Inventoteca/DisplayErgonomia/Fotos/Ensamblando_display/20210406_200713.jpg

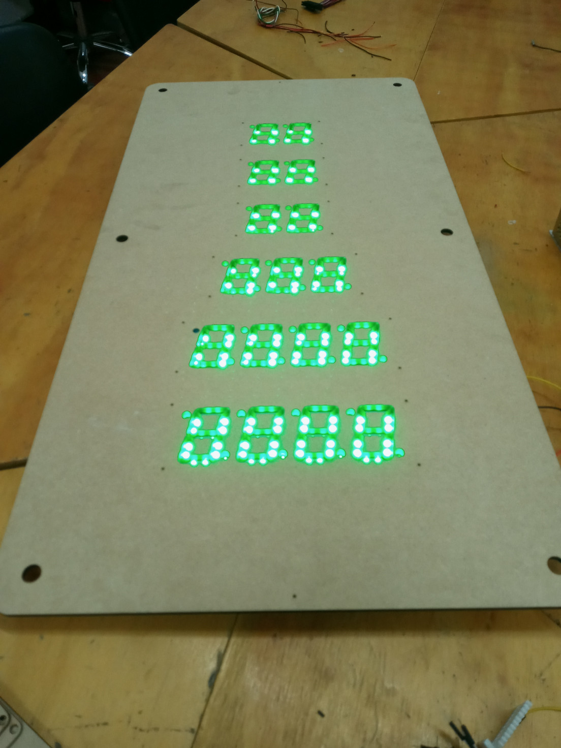
Fotos/Ensamblando_display/20210406_200713.jpg
