Inventoteca/DisplayErgonomia/Fotos/Ensamblando_display/20210407_082006.jpg

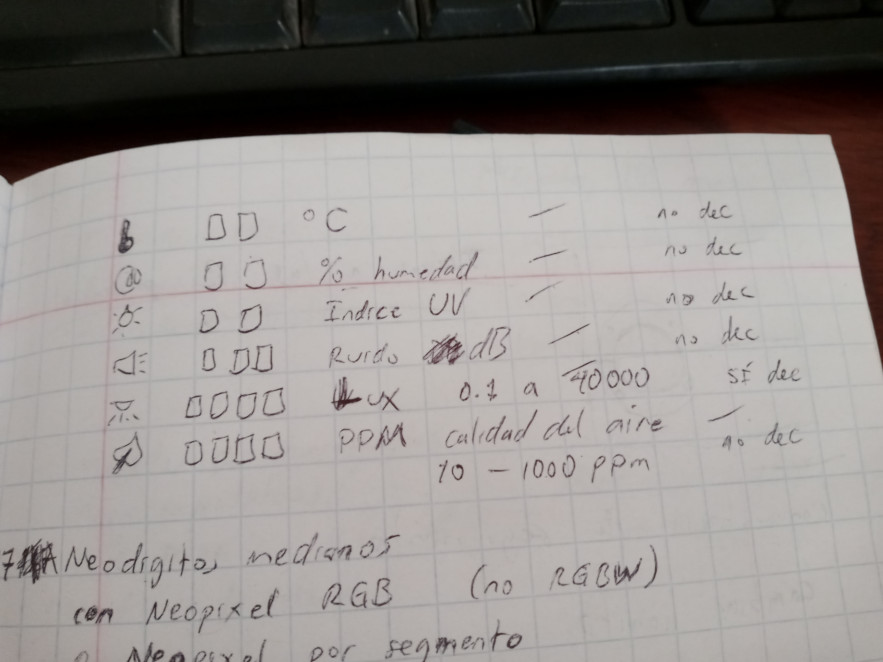
Fotos/Ensamblando_display/20210407_082006.jpg
