Inventoteca/DisplayErgonomia/Fotos/Ensamblando_display/20210408_172135.jpg

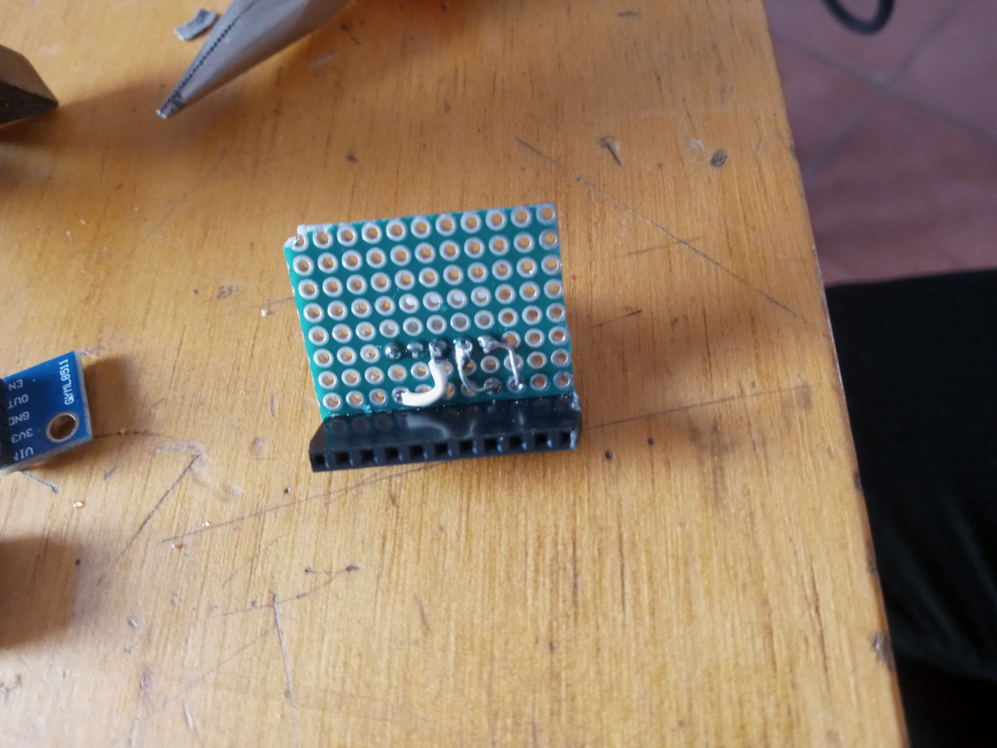
Fotos/Ensamblando_display/20210408_172135.jpg
