Inventoteca/DisplayErgonomia/Fotos/Ensamblando_display/20210409_184943.jpg

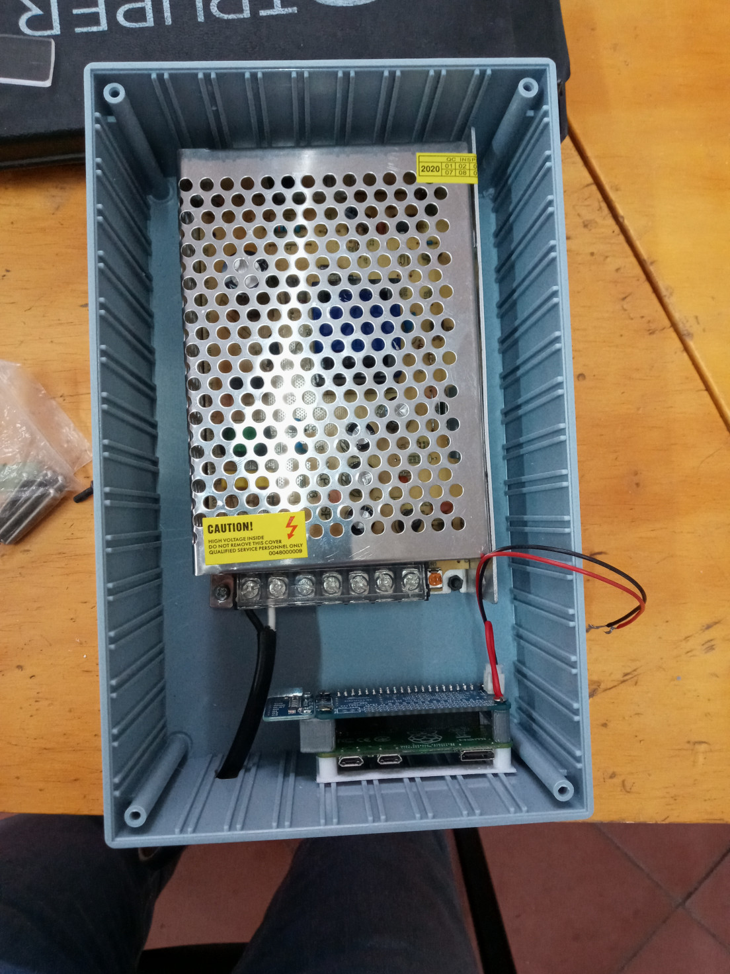
Fotos/Ensamblando_display/20210409_184943.jpg
