Inventoteca/DisplayErgonomia/Fotos/Ensamblando_display/20210412_164515.jpg

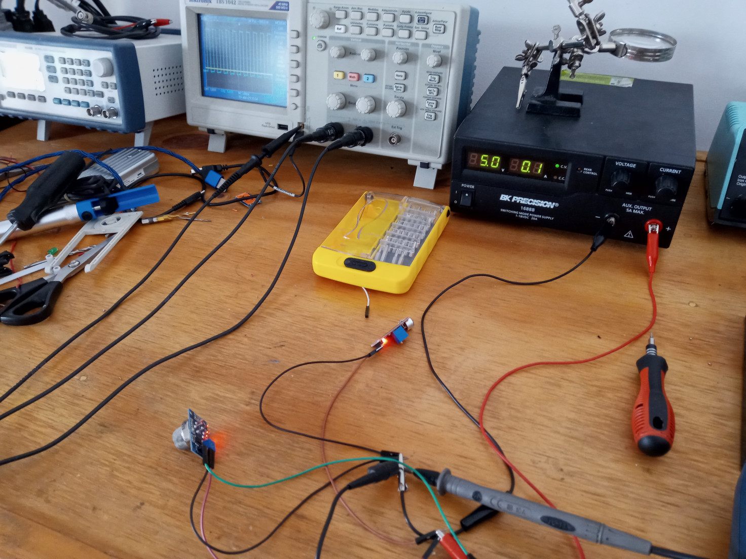
Fotos/Ensamblando_display/20210412_164515.jpg
