Inventoteca/DisplayErgonomia/Fotos/Ensamblando_display/20210412_164532.jpg

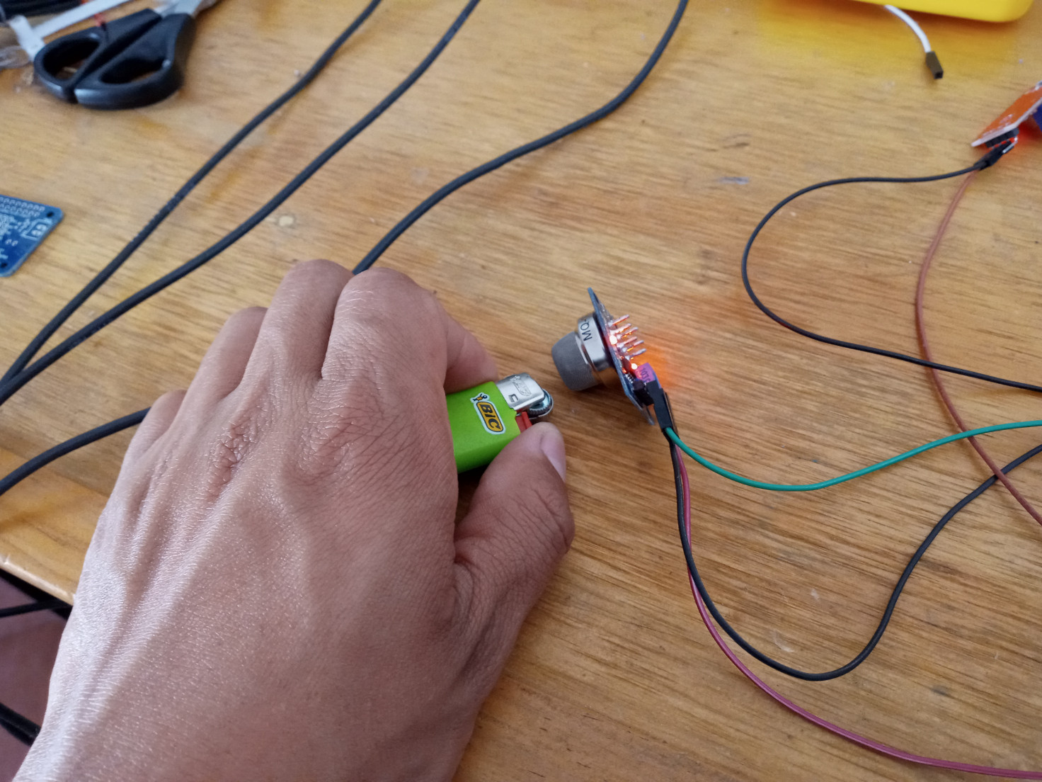
Fotos/Ensamblando_display/20210412_164532.jpg
