Inventoteca/DisplayErgonomia/Fotos/Ensamblando_display/20210413_124607.jpg

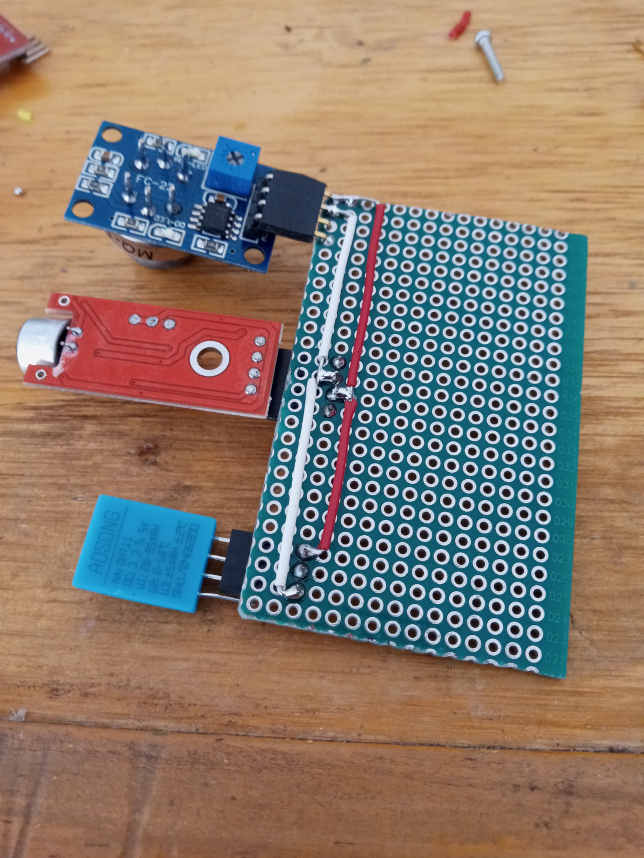
Fotos/Ensamblando_display/20210413_124607.jpg
