Inventoteca/DisplayErgonomia/Fotos/Ensamblando_display/20210414_124348.jpg

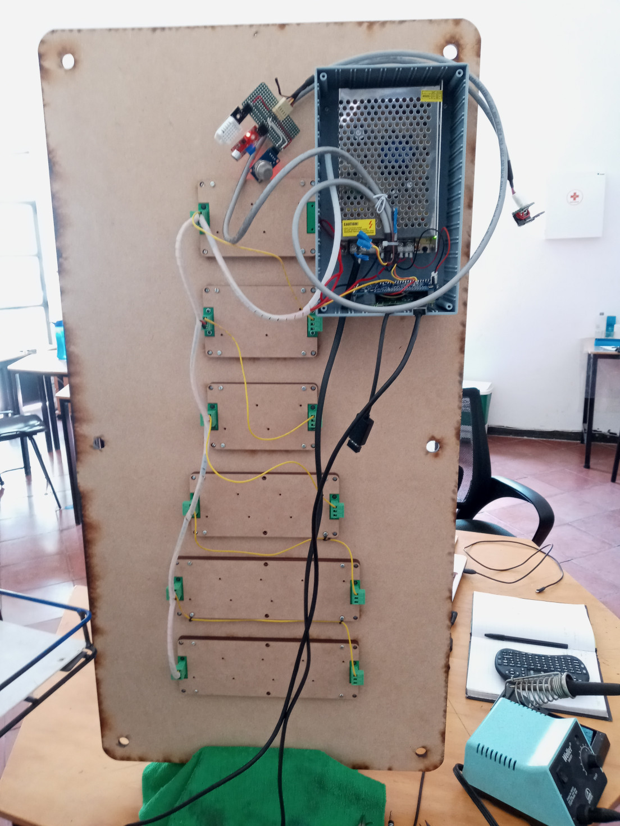
Fotos/Ensamblando_display/20210414_124348.jpg
