Inventoteca/DisplayErgonomia/Fotos/Ensamblando_display/20210415_141105_HDR.jpg

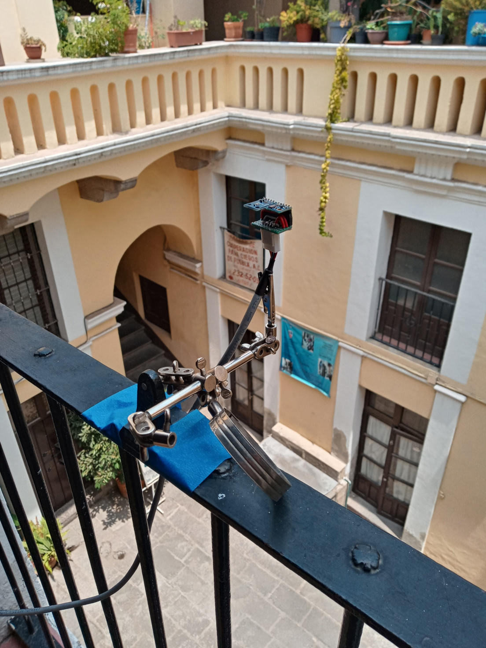
Fotos/Ensamblando_display/20210415_141105_HDR.jpg
