Inventoteca/DisplayErgonomia/Fotos/Ensamblando_display/20210415_141118.jpg

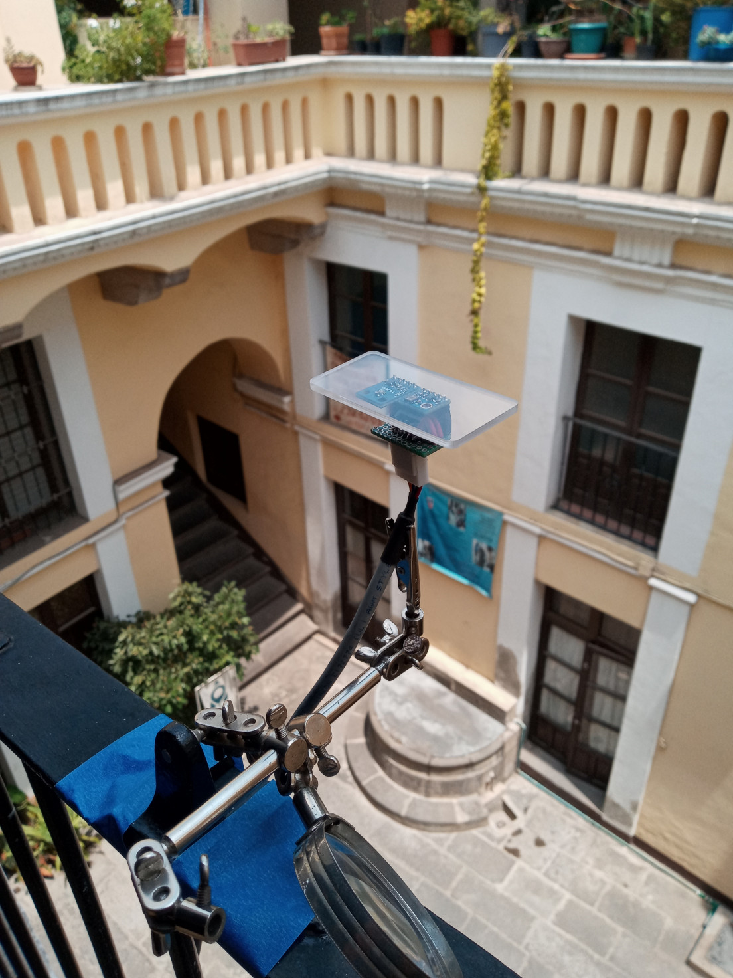
Fotos/Ensamblando_display/20210415_141118.jpg
