Inventoteca/DisplayErgonomia/Programa/Panel_esp32_board_cruz_dias/system.h

#ifndef SYSTEM_H
#define SYSTEM_H

#include <Arduino.h>
#include <ArduinoJson.h>
#include "pines.h"
#include "filespiffs.h"
#include <Arduino.h>
#include <esp_task_wdt.h>
#include "display.h"
#include "firebasedb.h"
#include "wifiservice.h"
//#include "clock.h"
#include "loraservice.h"

//15 seconds WDT
#define WDT_TIMEOUT 15


extern bool factory_press;
extern unsigned long factory_time;
extern unsigned long prev_factory_time;
//extern bool reset_time;
extern bool smart_config;
extern bool taskCompleted;
extern byte localAddress;     // address of this device
extern unsigned long mainRefresh;
extern unsigned long mainTime;
extern const uint32_t connectTimeoutMs;
extern unsigned long  s_timestamp;
extern int buttonState;
extern unsigned long tiempoInicio; 

void IRAM_ATTR factory_reset3();
void reset_config();
void check_reset();
//void neoConfig();
bool strToBool(String str);
float mapfloat(float x, float in_min, float in_max, float out_min, float out_max);
void loadConfig();
//void prepareData();

#endif
