Inventoteca/DisplayErgonomia/Programa/Panel_esp32_board_cruz_dias/wifiservice.h

#ifndef WIFISERVICE_H
#define WIFISERVICE_H


#include <WiFi.h> //import for wifi functionality
//#include "display.h"
#include "system.h"

//extern const uint32_t connectTimeoutMs;
//extern unsigned long  s_timestamp;
extern bool correct;
extern int wifi_trys;
extern boolean isSaved;

void WiFiEvent(WiFiEvent_t event, WiFiEventInfo_t info);
void Wifi_disconnected(WiFiEvent_t event, WiFiEventInfo_t info);
void checkServer();
void websocketInit();
void neoConfig();

#endif 
